HBDrew/PFD-and-AHRS/Docs/CONTROL_LOGIC_MAP.md

# TruTrak Vizion — Control Logic Map (v0.1)

**Status:** Working draft / reverse-engineering in progress
**Purpose:** Behavioral specification and test oracle for a modern, drop-in
replacement for the 2‑1/4" round and flat‑pack Vizion autopilot.
**Source of truth:** `TT AP Sources/` (Freescale 68HCS12 assembly, DigiFlight /
Sorcerer / Vizion‑380 lineage, version era ≈ A.43, 2003–2011).

> Citations below are `File:line` against the uploaded `TT AP Sources/` tree.
> Line numbers are from the version reviewed and should be re-verified when the
> sources are vendored into this repo.

**Companion deep-dives:**
- [`VERTICAL_CONTROL_LAWS.md`](VERTICAL_CONTROL_LAWS.md) — vertical axis in full
- [`STEPPER_OUTPUT_STAGE.md`](STEPPER_OUTPUT_STAGE.md) — command→phases servo chain
- [`SERVO_TORQUE_CONTROL.md`](SERVO_TORQUE_CONTROL.md) — torque/current control
- [`EEPROM_PARAMETER_MAP.md`](EEPROM_PARAMETER_MAP.md) — persisted parameter set

---

## Source provenance & build target (important)

This is a **single unified TruTrak codebase, target-selected at build time** — the
same source historically built DigiFlight II, **Sorcerer**, Model 100, RV-10AP and
Vizion (changelog: "v2.09 Merge the vertical mode code DFII/Sorcerer"). The shared
engine (`DFCMain.asm`, `DFC_IRQ.asm`, `p20Hz.asm`, `AD7714.asm`, `EEPROM.asm`, …)
contains **all** the control logic for every product, including Sorcerer.

**What selects a product is the per-target `Switches.asm`** (INCLUDEd at build):
it sets `PRODUCT_ID`, form-factor flags, `NAVMODE`, the switch/display layout and
pin maps, and *macro-generates* the `LM_*`/`VM_*` mode constants. This package
ships **only two target files, both Vizion 380**:

| Target file | PRODUCT_ID | Name |
|---|---|---|
| `Vizion 380 Flat/Switches.asm` | 1 | `[VZ380F]` |
| `Vizion 380 Round/Switches.asm` | 49 | `[VZ380R]` |

There is **no `Sorcerer/Switches.asm`** in this package. Sorcerer build knobs are
still visible (`EEDEFINES.h` `SORCERERNUMBER` calibration sets; an `IFDEF SKYPILOT`
path), but the Sorcerer *target configuration* (its product ID, panel switch
matrix, display driver, pin assignments) is not included.

**Consequence for this spec:**
- The **mode encodings and all control laws are target-independent** (same
  macro-generated constants, same math) — they apply to Sorcerer unchanged.
- **Target-specific citations here reflect the Vizion 380 Flat build** — notably
  pin/port maps (e.g. `MC33291` on `PTH.3`) and the switch/display layout. A
  Sorcerer (or other) target could differ in those.
- Building/analyzing the Sorcerer *target* would require its own `Switches.asm`.
  Open item: obtain it, then diff against the two VZ380 targets to enumerate the
  pin/switch/display/feature deltas.

---

## 0. Design intent for the revival (decisions locked)

These constraints frame every entry in this document. The map exists to make a
**behavioral port** possible, not a redesign.

| # | Decision | Rationale |
|---|---|---|
| D1 | **Preserve the rate-based inner loop.** Command a *turn rate* / *pitch rate*, close the inner loop on a rate signal. | Proven, robust, drives a stepper-through-slip-clutch well, and is the basis of "behaves like a Vizion." |
| D2 | **Attitude is a bounded *protection* layer only** — bank/pitch limiting, envelope, wings-level recovery. Never the primary control reference. | Keeps cost low, keeps the box source-agnostic, avoids re-tuning the whole feel. |
| D3 | **Keep the stepper servo drive.** Inherit the installed plant (stepper + clutch + cable + airframe) and harness/connector. | Required for true drop-in; the output stage ports over largely intact. |
| D4 | **Talk to anything.** Preserve all existing steering/deviation inputs (RS‑232 NMEA, ARINC‑429, discrete/analog CDI). | Rate-command interoperates with any GPS/EFIS that emits a steering or deviation signal. |
| D5 | **Preserve the tuned parameter set.** Gains encode years of flight tuning. | The port must carry gains + units forward verbatim, then re-scale deliberately. |
| D6 | **Ship setup UNLOCKED.** Remove the `EnableSettings == 10` gate — all setup menus directly accessible (via a modern menu, no button-hold handshake). | Baseline is **PV.40**; drop the "secret code." See "Setup-mode access" below. |

**Baseline: PV.40 (`pv.40` branch)** — chosen per
[`BASELINE_COMPARISON_PV40_vs_VZ15.md`](BASELINE_COMPARISON_PV40_vs_VZ15.md).

### Setup-mode access (the "secret code") — D6

PV.40 gates the advanced setup menus behind a parameter `EnableSettings`
(EEPROM `$0C`, def. `ENABLESETTINGS`). `DFCMain.asm:887` `enterSetup`:

- Knob pressed → **basic** setup (`EM_OFF`).
- `EnableSettings == 10` **and** hold **TRK/MODE** → lateral setup (`EM_LAT_FIRST`).
- `EnableSettings == 10` **and** hold **ALT** → vertical setup (`EM_VERT_FIRST`).
- `EnableSettings != 10` → locked (`noModeEvent`).

Default builds ship `ENABLESETTINGS = 0` (locked); **RV10 & Cessna-172 (certified)
ship `= 10` (unlocked from factory)** — hence those units felt "open." `S1_DIAG`
(diagnostics, `EM_DIAG`) is a separate gate.

**Revival:** delete the `CPD #10 / BNE` gate so setup is always reachable. (To
unlock a stock PV.40 binary on the bench: write `10` to EEPROM `$0C`.)

Target processing: modern Cortex‑M4F/M7 class MCU (FPU) → retire hand-rolled
fixed-point and the assembly RTOS in favor of C + float + small RTOS/superloop,
**while preserving the control-law structure and gains**.

---

## 1. System architecture (as-built)

Hand-written assembly on a Freescale 68HCS12 (16-bit, banked/paged flash), with
a **preemptive priority RTOS** written in assembly.

```mermaid
flowchart TB
  subgraph SENSE[Sensing]
    RG[Rate gyros: roll/pitch/yaw<br/>rollValue 163.84 cnt/deg/s]
    AD[Air data: IAS, Altitude, iVSI]
    GPS[GPS: track, gnd speed, xtrk, brg/dist]
    ARINC[ARINC-429 in: 121 roll-steer,<br/>320 mag hdg, 325 roll angle, alt]
    CDI[Analog/discrete CDI + rate]
  end
  subgraph EST[Estimation]
    DG[Electronic DG<br/>4-byte fraction-of-circle]
    MAG[magCircle]
    FILT[20 Hz filters, iVSI, LPF_1]
  end
  subgraph LOGIC[Mode logic]
    SM[Lateral + Vertical<br/>mode state machines]
  end
  subgraph LAW[Control laws]
    LAT[calcCommand -> turnCmd<br/>100 = 1 deg/s]
    VRT[vertical -> pitchCmd<br/>100 = 1 deg/s]
  end
  subgraph OUT[Servo output stage]
    RV[SetRollVel / SetPitchVel<br/>vel+pos, 2-pole LPF, activity,<br/>hysteresis, backlash comp]
    DRV[Stepper drive<br/>legacy DAC/PWM -> CAN motor msg]
  end
  SENSE --> EST --> LOGIC --> LAW --> OUT --> Steppers
  RG --> LAW
```

**Concurrency (RTOS):** `Kernel.inc` defines a TASK struct (linked ready list,
timer wakeup list, per-task page register), semaphores (`MAX_SEM`), and
`createTask/signal/wait/setPri`. Tasks coordinate through semaphores rather than
one superloop.

| Task / ISR | Rate | Role |
|---|---|---|
| Timer ISR (`tim_int`) | ~250 Hz (4 ms) | Servo velocity loop, switch debounce, timers |
| 20 Hz filter (`Start20Hz`, `p20Hz.asm`) | 20 Hz | Low-rate filtering, GPSS buffer, mode housekeeping |
| Main loop (`mainLoop`, `DFCMain.asm`) | event/10 Hz | Mode logic, display, `calcCommand` |
| RS‑232 out (`StartOutput`) | streaming | Status/telemetry |
| GPS monitor (`GPSMonitor*.asm`) | per-sentence | Parse NMEA / protocol |
| CAN (`CAN.asm`) | per-msg | Smart-servo motor messages |
| Talker (`Talker.asm`) | event | Audio annunciation |

*Timer tick inferred from `DFC_IRQ.asm` "number of 4mSec periods" comments — verify exact prescaler.*

---

## 2. Mode model (the `mode` byte)

> **PV.40 baseline update:** on the chosen PV.40 baseline, `VERTICAL_MASK` is
> **`$F0`** (vertical field = bits 4–7) and there are extra modes — lateral
> `LM_DYNON/LM_AEP/LM_ASPEN`, vertical `VM_DYNON/VM_EXT_ALT`. See
> [`PV40_BASELINE_ADDITIONS.md`](PV40_BASELINE_ADDITIONS.md) §1–2. The encoding
> below reflects the 2011 baseline and still holds for the common modes.

A single byte `mode` is bit-packed (`Vizion 380 Flat/Switches.asm:38-63`):

```
 bit 7   bits 6..4          bits 3..0
 [ E ] [ vertical mode ] [ lateral mode ]
   |         |                  |
   |         |                  +-- LATERAL_MASK = $0F
   |         +--------------------- VERTICAL_MASK = $70
   +------------------------------- entry/display-mode flag ($80)
```

### 2.1 Lateral modes (`LM_*`, sequential 0..10)

| Val | Mode | Meaning |
|----:|---|---|
| 0 | `LM_NONE` | AP off; initial until CWS or ENT |
| 1 | `LM_CWS` | AP off; CWS pressed, capturing gpsTrk |
| 2 | `LM_TRK` | Track mode — follow selected ground track (**universal fallback**) |
| 3 | `LM_DG` | External DG/HSI — follow external turn command |
| 4 | `LM_GPSNAV` | GPS NAV, CDI centered to waypoint |
| 5 | `LM_GPSPOST` | GPS NAV, near/past waypoint |
| 6 | `LM_GPSS` | GPS Steering — follow ARINC/RS‑232 bank command |
| 7 | `LM_NAV_PRE` | Intercepting NAV CDI via calculated vector |
| 8 | `LM_NAV_POST` | NAV CDI captured, hold centered (low gain) |
| 9 | `LM_REV_PRE` | Like NAV_PRE, steer *away* from needle |
| 10 | `LM_REV_POST` | Like NAV_POST, steer *away* from needle |

Free-gyro **wing-leveler / bank-hold** is a sub-behavior of the `selTrk` path
(`DoSelTurn`) when no GPS/mag reference is present and `selBank ≠ 0`
(`DFCMain.asm:1688`).

### 2.2 Vertical modes (`VM_*`, value = index << 4)

| Mode | Meaning |
|---|---|
| `VM_NONE` | No vertical mode |
| `VM_HOLD` | Altitude hold |
| `VM_AS_SELECT` | Climb/descend to selected alt at selected airspeed |
| `VM_VS_SELECT` | Climb/descend to selected alt at selected ft/min |
| `VM_SPEED` | VS entered manually while in hold |
| `VM_CAPTURE` | Following glideslope (GS) |
| `VM_VNAV` | Selected alt at selected distance |
| `VM_GPSS` | External unit giving pitch/vertical command (VGPSS) |

---

## 3. Lateral mode state machine

Events come from buttons/knob/timeouts via the action table
(`DFCMain.asm:383-399`): `altAction` (AP), `GPSSAction` (GPSS), `NAVAction`,
`REVAction`, `TRKAction`, `modeAction`, `rotAction` (knob turn),
`knobAction` (ENTER), `revertAction` (idle timeout), `vsUp/vsDn/HOLD/ASEL/VNAV`.

```mermaid
stateDiagram-v2
  [*] --> OFF
  OFF: LM_NONE (AP off)
  CWS: LM_CWS (capturing track)
  OFF --> CWS: CWS switch
  CWS --> TRK: release (capture gpsTrk)
  OFF --> TRK: AP engage

  TRK: LM_TRK (fallback home)
  TRK --> TRK: knob rotate (set selTrk)
  TRK --> GPSS: GPSS btn (if steer cmd valid)
  TRK --> DG: ext DG selected
  TRK --> NAV_PRE: NAV btn
  TRK --> REV_PRE: REV btn
  TRK --> GPSNAV: GPS NAV armed

  GPSS --> TRK: steer cmd lost (snapshot DG -> selTrk)
  GPSNAV --> GPSPOST: near/past waypoint
  GPSNAV --> TRK: guidance lost
  GPSPOST --> TRK: guidance lost

  NAV_PRE --> NAV_POST: CDI intercept
  NAV_POST --> TRK: NAV lost
  REV_PRE --> REV_POST: CDI intercept
  REV_POST --> TRK: NAV lost

  DG --> TRK: ext DG lost / mode change
  TRK --> OFF: disconnect
  GPSS --> OFF: disconnect
  NAV_POST --> OFF: disconnect
```

**Invariants worth preserving verbatim:**

- **TRK is the safe harbor.** Any loss of GPSS/GPS‑NAV/NAV guidance snapshots the
  current DG heading into `selTrk` and reverts to `LM_TRK`
  (`DFCMain.asm:1660-1670`, `lostLatGuidance`). The aircraft keeps flying its
  current heading rather than dropping the servo.
- **Lateral↔vertical coupling:** setting *any* lateral mode while in `VM_CAPTURE`
  (glideslope) forces vertical to `VM_HOLD` (`SetLatMode`, `DFCMain.asm:5198`).
- `SetLatMode` toggles only the lateral nibble and always clears the entry-mode
  bit — modernized code must keep mode fields independent.

---

## 4. Lateral control law (`calcCommand`, `DFCMain.asm:1233`)

Output is `turnCmd` (signed, **100 = 1 °/s**, positive = turn right),
`DFC_IRQ.asm:203`. The active branch depends on lateral mode:

1. **Selected-track / DG (`DoSelTurn`, `DoDGTurn`)**
   - Error = `selTrk − DG` in circle units.
   - Low-pass filter the error (`LPF_1`, `TrkError_LPF`), filter constant
     **scheduled on IAS** (`DGCONST` from `currIAS`, `DFCMain.asm:1454+`).
   - Add a **track-rate (derivative) term**, zeroed when |error| > 45°
     (`$2000`/`$E000` guards) to avoid nonsense during large captures.
   - Gain via lookup `TRKRATEGAINtbl`; convert to command by ×`#3584/65536`
     (≈ 7/128) → command 300 at 30° error.
2. **GPSS (`DoGPSSTurn`, `DFCMain.asm:1560`)**
   - Take external bank command `gpssRoll`, scale by `gpssGain/8`, saturate to
     ±8192.
   - Add a rate term now **airspeed-scheduled**: gain = `TAS[kt·8]/60`
     (`DFCMain.asm` 2.36B block), saturate to ±8192.
   - If ARINC label 325 (roll angle) is present, form a closed-loop bank error
     (`DoGPSSErrorTurn`).
3. **NAV / REV (LOC/VOR)** add a **rate (CDI-movement) term** beyond the bank
   limiter (`addNavRate`, `DFCMain.asm:~1990+`): LOC uses `locRateGain`; VOR uses
   4× fixed radio rate with a 1 °/s clip for station passage; REV reverses sense.
4. **Cross-track intercept geometry:** intercept angle = `arcSin(64·xTrkErr[nm]/gs[kt])`,
   `xTrkErr` clipped to 127 nm to prevent overflow (`DFCMain.asm:2794`).

**Bank limiter** (applied to the command, not attitude), `DFCMain.asm:1782-1830`:

| `MaxBank` | Turn-cmd clamp | ≈ bank @ 200 kt |
|---|---|---|
| 0 (LO) | 225 | ~22° |
| 1 (MED)| 300 | ~25° |
| 2 (HI) | 375 | ~28° |

GPSS uses a separate `gpssMaxBank` (~25°).

---

## 5. Vertical control law (summary)

> **Full treatment:** [`VERTICAL_CONTROL_LAWS.md`](VERTICAL_CONTROL_LAWS.md) —
> the VS-rate pipeline, iVSI estimator, `pitchAdj` trim integrator, all modes
> (ALT/VS/AS-hold/VNAV/GS/VGPSS), envelope protection, and two comment-vs-code
> discrepancies to reproduce.

- **ALT HOLD:** `altErr = selAlt − currAlt`, scaled by user `altGain` (0..8),
  combined with **iVSI** (integrated/inferred vertical speed, computed
  proportional to altitude), plus turbulence filtering → `pitchCmd`.
- **VS / VS_SELECT:** fly a selected ft/min toward selAlt.
- **VNAV:** compute required VS to reach `selAlt` at `selDist`.
- **GS CAPTURE (`VM_CAPTURE`):** arm/couple timers (`gsTimer`, `vgsTimer`),
  go-around pitch-up on leaving coupling (`gaTimer`); auto-drops to HOLD on
  lateral mode change.
- **VGPSS (`VM_GPSS`):** vertical steering from ARINC deviation.

---

## 6. Servo output stage (`SetRollVel` `DFC_IRQ.asm:1888`, `SetPitchVel`)

This is the part that ports over most directly (D3). Per axis:

1. Scale commanded velocity by **activity setting** (`latGain`/`vrtGain`, 0..12,
   log-encoded offset-by-6) via `actTable`.
2. Saturating multiply (hand-rolled overflow guard `rOVF`).
3. **2-pole low-pass** (`rv1`, `rv2`).
4. **Servo velocity limiter** (`servoLimit`).
5. **Deadzone / hysteresis:** 50-count hysteresis to suppress noisy dither.
6. **Lost-motion / backlash compensation:** on a commanded direction reversal,
   inject `16·sign(dir)·lostMotion` for ~400 ms (`rDZ_*`). This compensates gear
   backlash in the stepper/clutch drive — **must be reproduced.**
7. Result → `rollVel`/`pitchVel`; **position = ½∫velocity** (`rollPos`/`pitchPos`).
8. Emit to drive — **this build drives BOTH paths every servo tick, in parallel**
   (confirmed):
   - **Stepper (legacy, the one we need for 2‑1/4"/flat-pack):** `DoMotors`
     (`DFC_IRQ.asm:2193`, called from the ISR at `:3059`) integrates velocity →
     `rollPos`/`pitchPos`, indexes the 8-entry **gray-code phase table**
     `grayTable` (half-step aware), merges roll (high nibble) + pitch (low
     nibble) into one byte, and shifts it out over SPI0 to an **MC33291 octal
     low-side driver** that energizes the stepper phases. Includes a v2.20c
     inrush-limiting sequence on 0→1 phase transitions (`SERVO_PORT` holds the
     previous pattern for ~1 µs).
   - **CAN smart-servo (later designs):** `MotorCANMsgBuffer` populated in
     `SetRollVel` + `DoMotors`; transmitted via `CAN_TxMessage`
     (`CAN.asm:598`, called from `DFCMain.asm:1096/8789/8888`).
   - **Oldest analog drive retired:** `DAC_67Out` servo-voltage path is commented
     out; the DAC survives only for the yaw-damper output.

> **Full bit-level treatment of this stage:** see
> [`STEPPER_OUTPUT_STAGE.md`](STEPPER_OUTPUT_STAGE.md) — inner rate loop,
> velocity conditioning (activity table, LPF, limiter, hysteresis, backlash),
> position integration, gray-code phase output, MC33291 mapping, and the
> modern-hardware reproduction plan.
>
> **Backward-compat scheme (confirmed):** not a stepper-vs-CAN config switch —
> both drivers run unconditionally from the same velocity/position math each
> tick, and the airframe harness consumes whichever it is wired for. The `config`
> bits gate yaw damper / alt selector / ext-DG only, not servo type. **This is
> the correct both-worlds source version.** For the revival, replicate the
> stepper chain: **velocity → ½∫ position → gray-code phase table → phase
> driver** (MC33291 or modern equivalent).

---

## 7. Units & fixed-point dictionary

The single most portable asset. Every constant below must survive the port.

| Quantity | Representation | Notes |
|---|---|---|
| Heading / track / bearing | **circle units**: 65536 = 360° | `DG` is 4-byte fraction of circle; `BrgToCir`/`CirToHdg` convert |
| Turn / pitch command | signed, **100 = 1 °/s** | `turnCmd`, `pitchCmd` |
| Roll rate (gyro) | **163.84 counts/°/s**, signed | `rollValue` |
| Airspeed | **kt · 8** | `currIAS`, `currTAS` (since v2.16) |
| Altitude | **ft MSL**, signed (4 ms-bits = negative) | `currAlt`; `filterAlt` carries fraction |
| Baro | inHg · 100 | `baroSet` (2992 = 29.92) |
| Activity / gain | 0..12, **log offset-by-6** (6⇒×1, >6⇒×9/8, <6⇒×7/8) | `latGain`, `vrtGain` |
| Cmd→bank scale | `×3584/65536` (≈7/128) | 300 cmd ≈ 30° track error |
| GPSS saturation | ±8192 | repeated inline (candidate for one routine) |

---

## 8. Envelope protection & interlocks

The safety layer — where attitude protection (D2) will augment, not replace.

- **Airspeed envelope** (vertical modes, `DFCMain.asm:2325-2445`, `CAS_1:3702`):
  climbing won't allow IAS < `minAS` (stall guard); descending won't allow
  IAS > `maxAS` (overspeed). `absMaxAS = 399 kt`. `minAS` not enforced below
  ~50 kt actual (avoid ground false-trip).
- **MIN AS annunciation also drops the yaw damper** (`HISTORY` 2.19).
- **Gyro centering hold-off:** in TRK, when |command| > 250 for a sustained
  maneuver, set `turnTimer` (150 → ~30 s) so the roll gyro doesn't capture an
  offset mid-turn (`DFCMain.asm:1869+`). *This kludge is a prime candidate to
  replace with a real attitude reference under D2.*
- **Disconnect / CWS** paths; press-and-hold semantics (`cwsSem`, `yokeSem`).

**Modernization note (D2):** add attitude-based bank/pitch limiters and a
wings-level recovery as an outer *clamp* on `turnCmd`/`pitchCmd`, and replace the
`turnTimer` centering hack with attitude-referenced centering. Attitude never
becomes the command reference.

---

## 9. I/O & interfaces (for "talk to anything", D4)

| Interface | Direction | Content |
|---|---|---|
| RS‑232 NMEA (`GPSMonitor*.asm`) | in | GPS track, gnd speed, xtrk, brg/dist |
| ARINC‑429 (`arinc_int`) | in | 121 roll steering, 320 mag hdg, 325 roll angle, selected/baro alt |
| Analog/discrete CDI | in | LOC/VOR deviation + rate (`ATD0DR2H`) |
| External DG/HSI | in | `ATD0DR4H`, `dgGain` |
| RS‑232 status (`StartOutput`) | out | Mode/airspeed/trim telemetry |
| CAN (`CAN.asm`) | out | Smart-servo motor messages |
| Audio (`Talker.asm`) | out | Voice annunciation |
| Display + knob/buttons | i/o | UI |

---

## 10. Open questions / next revisions

- [x] **Servo drive:** RESOLVED — this build drives both the legacy gray-code
      stepper (MC33291/SPI) and CAN smart-servo in parallel every tick; harness
      picks. Confirmed correct both-worlds source. Revival targets the stepper
      chain (§6).
- [ ] Vendor the `TT AP Sources/` tree into the repo (or a ref/ subfolder) so
      citations resolve and diffs are traceable — confirm IP/licensing first.
- [ ] Full **parameter/EEPROM map** (`EEDEFINES.h`, `EEPROM.asm`): every gain,
      offset, limit with address + default + units.
- [ ] v0.2: complete **vertical** state machine + laws (VNAV, GS capture, VGPSS).
- [ ] Confirm timer-tick rate/prescaler (assumed 4 ms / 250 Hz).
- [ ] Enumerate exact button/event → transition guards from the action routines.
- [ ] Catalog target variants (Vizion 380 Flat/Round, Model 100, RV‑10) and their
      conditional-assembly differences.

## 11. Old → new mapping (guiding the port)

| As-built (68HCS12 asm) | Revival (Cortex-M4F, C) | Under decision |
|---|---|---|
| Rate gyros | MEMS IMU rate channels (better source, same law) | D1 |
| No attitude ref; `turnTimer` centering hack | AHRS attitude → protection clamps + centering | D2 |
| Hand fixed-point (circle units, kt·8) | float, but **keep gains & scaling documented** | D5 |
| Assembly RTOS + semaphores | small RTOS / timed superloop | — |
| DAC/PWM→CAN stepper drive | match installed-base drive exactly | D3 |
| Repeated inline saturation | one vetted `saturate()` | maintainability |
| Demo/`fMode` hooks in flight path | compiled out / separate build | safety |

---

*v0.1 — extracted from `TT AP Sources/`. Sections §5, §8, §10 flagged for
expansion. Treat every gain/threshold here as authoritative-to-verify against the
source before it drives code.*
