HBDrew/PFD-and-AHRS/Docs/ADSB_IN.md

# ADS-B IN — Traffic (and FIS-B weather) on the PFD

This document describes the ADS-B IN feature: how the display ingests
traffic, how to wire up the Nooelec NESDR Nano 2 dual-band receiver, and
what is implemented vs. planned.

## What it does

Live aircraft traffic is drawn on the moving-map inset of both displays
(Pi Zero MFD and Pi 4) as TCAS-style diamonds with a heading leader and a
relative-altitude data tag. Targets are colour-coded by threat:

| Colour | Class | Meaning |
|---|---|---|
| Cyan (hollow diamond) | other | has a position, outside the proximate envelope |
| Amber (filled) | proximate | within 6 NM **and** 1200 ft |
| Red (filled) | alert | within 3 NM **and** 600 ft, or the source flagged a traffic alert |

The data tag reads relative altitude in hundreds of feet with a trend
arrow, e.g. `+12↑` (1200 ft above and climbing), `−05↓` (500 ft below,
descending).

Toggle the layer at **Setup → Display → MAP LAYERS → TFC**.

## Architecture

The display side is **hardware-independent** — it speaks GDL90 over UDP,
the lingua franca of portable ADS-B receivers (Stratux, Sentry, GDL90
bridges). Nothing in the PFD knows about SDR dongles.

```
 1090ES  ── NESDR ──►  readsb ───────┐
                                     ├─ SBS-1 :30003 ─► adsb_gdl90_bridge.py ──┐
 978 UAT ── NESDR ──►  dump978-fa  ──┘  (978 traffic folds into readsb too)    │
                                                                              GDL90/UDP :4000
 Internet aggregator  ──►  adsb_internet_feed.py  ───────────────────────────►│  (any/all
 (airplanes.live / opensky, via Wi-Fi / Starlink)                             │   sources fan in)
                                                                              ▼
                                            shared/adsb.py  (ADSBClient: UDP listener,
                                            target table, staleness aging, snapshot)
                                                          │
                                            shared/gdl90.py (deframe + CRC + decode)
                                                          │
                              pfd.py _update_traffic()  → disp["traffic"]
                                                          │
                              moving_map.render(traffic=…) → diamonds
```

### Modules

| File | Role | Tested by |
|---|---|---|
| `shared/gdl90.py` | GDL90 framing (0x7E / byte-stuffing / CRC-16) + message decoders (Traffic 0x14, Ownship 0x0A/0x0B, Heartbeat 0x00, FIS-B uplink 0x07). Also an encoder for tests/bridges. | `shared/test_gdl90.py` |
| `shared/adsb.py` | `ADSBClient` threaded UDP listener (SSEClient-style counters), target table with aging, `relative()` range/bearing/rel-alt, `threat_level()`, `demo_targets()`. | `shared/test_adsb.py` |
| `tools/adsb_gdl90_bridge.py` | readsb/dump1090 SBS-1 (TCP 30003) → GDL90/UDP bridge using the encoder above. | `--selftest` |
| `tools/adsb_internet_feed.py` | Internet ADS-B aggregator → GDL90/UDP feed (test source + Starlink in-flight source). | `--selftest` |
| `tools/install_adsb.sh` | Installs rtl-sdr + **readsb** (1090) + the GDL90 bridge systemd unit. (978 via `install_dump978.sh`.) | — |

Because every source emits the same GDL90/UDP, they are interchangeable and
can even run side by side — a local SDR receiver, the SBS→GDL90 bridge, and
the internet feed all just fan into the one listener on :4000.

### Display wiring

`pfd.py` (both variants) starts an `ADSBClient` at boot when
`cs["adsb_enabled"]` is set, and once per frame calls `_update_traffic()`,
which snapshots the listener (or `adsb.demo_targets()` in `--demo`),
relativises each target against the current ownship fix, classifies its
threat, sorts nearest-first, and stores the result in `disp["traffic"]`.
`moving_map.render(traffic=…)` draws it, gated by `ds["map_show_traffic"]`.

Link diagnostics are mirrored into `cs["adsb_online"|"adsb_rx"|"adsb_err"|
"adsb_last_err"|"adsb_uplink"]` (runtime-only, not persisted).

## Hardware setup (Nooelec NESDR Nano 2 dual-band)

The bundle is two RTL-SDR dongles plus 978/1090 antennas. Run the receiver
on the display Pi, a dedicated Pi (a Pi 5 has ample headroom), or point the
display at an existing Stratux on the network.

```bash
sudo bash tools/install_adsb.sh       # rtl-sdr + readsb (1090) + GDL90 bridge
sudo bash tools/install_dump978.sh    # 978 UAT decoder + FIS-B weather bridge
sudo bash tools/enable_978_traffic.sh # fold 978 traffic into readsb's :30003
sudo reboot                           # so the DVB-T driver blacklist takes effect
```

Give each dongle a distinct USB serial so the decoders grab the right band:

```bash
rtl_eeprom -d 0 -s 1090          # dongle on the 1090 antenna
rtl_eeprom -d 1 -s 978           # dongle on the 978 antenna
```

The 1090 decoder is **readsb** (wiedehopf's installer) — `dump1090-fa` isn't
reliably packaged for current Raspberry Pi OS (Debian trixie / Pi 5). readsb is
pinned to the 1090 dongle via `RECEIVER_OPTIONS="--device 1090 …"` in
`/etc/default/readsb` and publishes SBS-1 on TCP 30003, which the bridge turns
into GDL90/UDP :4000. dump978 (serial `978`) decodes the 978 band.

> **Bringing up a fresh / dedicated receiver Pi?** See `BENCH_TEST_PI5_ADSB.md`
> for the full layered procedure (hardware → decoders → bridge → display), the
> LAN-broadcast gotcha, and the two failures seen on a real Pi 5 bring-up.

Verify:

```bash
systemctl status adsb-gdl90.service
python3 tools/adsb_gdl90_bridge.py --selftest
```

## Testing without hardware

```bash
python3 shared/test_gdl90.py     # decoder unit tests
python3 shared/test_adsb.py      # listener + geometry + UDP loopback
python3 pi4/pfd.py --demo --sim  # synthetic traffic orbits the demo aircraft
```

### Testing with real internet data

`tools/adsb_internet_feed.py` pulls live aircraft from a public ADS-B
aggregator and emits them as GDL90/UDP — so you can see *real* traffic on
the map with no SDR and no Pico. Run the display and the feed together:

```bash
# terminal 1 — the PFD (demo flies the Sedona pattern; live traffic wins
# over the synthetic targets, so point the feed at the demo location)
python3 pi4/pfd.py --demo --sim

# terminal 2 — feed real traffic within 80 NM of the demo position
python3 tools/adsb_internet_feed.py --lat 34.8697 --lon -111.7610 --radius 80
```

Point it somewhere busy (`--lat 33.94 --lon -118.40` for KLAX) to stress the
renderer with dozens of targets. Sources: `airplanes_live` (default),
`adsb_lol`, `adsb_fi`, `opensky` — none need an API key.

The "live wins over demo" rule (`_update_traffic`) means any real source —
internet feed, dump1090 bridge, or hardware receiver — overrides the
synthetic demo targets the moment frames start arriving.

## In-flight over Starlink / cabin Wi-Fi

With internet in the aircraft, the same feed becomes a real traffic source —
no receiver required. Run it on the display Pi and have it re-centre on your
own GPS so the query box follows the flight:

```bash
python3 tools/adsb_internet_feed.py --follow-ahrs http://192.168.4.1/events --radius 60
```

(Or install it as a systemd service alongside `adsb-gdl90.service`.)

**Advisory only.** Internet traffic depends on ground-station coverage and
connectivity — it lags a few seconds, has coverage gaps, and won't reliably
include UAT-only / non-transponder aircraft. It is **not** a substitute for
see-and-avoid or a certified traffic system. A local SDR receiver (the
Nooelec) gives better own-ship-relative traffic because it's direct
line-of-sight and works without internet; treat the internet feed as a
convenient backup / test source. Keep the poll interval ≥ 1 s out of
courtesy to the free aggregators.

## Implemented vs. planned

**Implemented (V5.4):**
- GDL90 decode + UDP ingest + target management (tested)
- Relative geometry + TCAS-style threat classification
- Traffic diamonds on both moving maps + TFC layer toggle
- dump1090 → GDL90 bridge + receiver installer
- Demo traffic generator

- Internet traffic feed (`tools/adsb_internet_feed.py`) — no-hardware test
  source and Starlink/cabin-Wi-Fi in-flight source; live traffic overrides
  the demo targets automatically.
- Traffic declutter — altitude-band (±2k/5k/10k) and range (5/10/20/40 nm)
  filters on Setup → Display; alert-class threats always survive.
- **Weather — METARs.** `shared/wx.py` polls aviationweather.gov for the
  current **map view** (not just the aircraft) — `WxClient` takes a
  `view_fn -> (lat, lon, radius)` and re-fetches when you pan far enough,
  zoom, or the periodic refresh is due (debounced so a drag doesn't spam the
  API). Query radius scales with zoom (`WX_RADIUS_ZOOM_K`, clamped
  `WX_MIN/MAX_RADIUS_NM`), so panning/zooming over CONUS loads weather for
  wherever you're looking. Flight-category station dots (green VFR / blue
  MVFR / red IFR / magenta LIFR) render on both maps. Tap a dot on the MFD
  for the decoded readout. Source-agnostic `disp["weather"]`.
- **Overlay quick-cycle** (`shared/mapoverlay.py`, unit-tested). Traffic
  stays on always (safety); a single on-map control cycles the heavy
  overlays one-at-a-time to keep the map readable and CPU low:
  **Airspace → Traffic → METAR → Winds → NEXRAD** (labels ASP / TFC / MET / WND / NEX).
  "Traffic" (TFC) is the traffic-only state — no heavy overlay added;
  traffic + your base map still show. On the Pi Zero MFD it's the button
  under the RNG label; on the Pi 4 inset it's the **bottom-left corner**
  (label shows the current state). Both drive the same `ds["map_show_*"]`
  booleans the Setup → Display pills (MET / NEX / ASP) use, so they stay
  consistent. The weather poller only runs while METAR/NEXRAD is the active
  overlay — no CPU/network spent on weather you're not looking at.

- **Weather — NEXRAD raster** (`shared/nexrad.py`). Composite reflectivity
  from the Iowa Environmental Mesonet WMS (free, no key), fetched for the
  current map view (same `view_fn` as METARs) and only while the NEXRAD
  overlay is active. Rendered **north-up** (no per-frame rotation — lowest
  CPU; aligned in north-up mode), georeferenced to its lat/lon bbox, blitted
  semi-transparent under the symbols. The scaled/dimmed surface is cached, so
  the per-frame cost is one blit; it's re-decoded only when a new image
  arrives (~5 min) or the zoom changes.
- **Weather declutters the base map.** While METAR, NEXRAD, or winds is the
  active overlay, the terrain tint and obstacle/tower symbols are suppressed —
  cleaner weather picture, and skipping the tint build is the biggest CPU
  saving the inset has.
- **Weather — TAF / AIRMET / SIGMET / NOTAM readouts.** Tapping a station on
  the MET page opens a picker with **METAR / TAF / AIRMET / SIGMET / NOTAM**
  tabs (scrollable, nearest-first, ON-ROUTE flags). TAFs + AIRMET/SIGMET come
  from aviationweather.gov (AWC); graphical AIRMET/SIGMET hazard polygons are
  shaded and tappable. NOTAMs come from the **FAA NMS-API** (two-step OAuth2;
  preprod `api-staging.cgifederal-aim.com`, prod `api-nms.aim.faa.gov`) — needs
  a `client_id`/`client_secret` (**NOTAM KEY** / **NOTAM SECRET**) plus a
  **NOTAM ENV** (preprod default) entered on the Connectivity screen; absent a
  key the NOTAM fetch is a harmless no-op. NOTAMs use their own **tight,
  zoom-following query radius** (`NOTAM_MIN/MAX_RADIUS_NM`, ~10–40 nm) rather
  than the wide weather radius, so a tap over a metro returns a local handful
  rather than every NOTAM for hundreds of miles. **Shared over screen-sync**
  (`KIND_NOTAMS`): one keyed display feeds NOTAMs to peers that have no key, and
  the key itself can be **pushed to every display** (`KIND_NOTAMCREDS`) by
  entering it once in Connectivity — same model as winds aloft.
- **Weather — winds aloft (WND).** GFS pressure-level winds from Open-Meteo
  (`gfs025`, free, no key), capped at 18,000 ft. Cached as a national grid
  split into 6 zones, fetched on the ground one zone at a time, written to disk
  (`data/winds/conus_winds.json`), and re-pulled only when a zone is > 3 h
  stale. Rendered as standard wind barbs + temperature at a selectable altitude
  (3k–18k) and forecast time (NOW/+Nh). **Shared between displays** over the
  screen-sync UDP link (`KIND_WINDS`): one display with internet feeds the
  whole panel so the others make zero Open-Meteo calls (per-IP rate-limit fix).
- **Traffic status + collision alert.** On-screen `ADS-B <mode> R<n> I<n>` and
  `WX <mode> R<n> I<n> <age>` status lines (tap to cycle RADIO/AUTO/INET); a
  flashing red **TRAFFIC** banner and (Pi 4) a **"Traffic, Traffic"** voice
  callout when a new target enters the alert envelope (≤ 3 NM and ≤ 600 ft),
  edge-triggered, rate-limited. Pi Zero is visual-only.

### FIS-B (978 UAT) weather — radio-primary, internet-bonus

Weather over the radio, no internet needed — the same source model as traffic.
The 978 dongle (serial `978`) is decoded by **dump978**; its raw uplink frames
(`+…` lines) are bridged to GDL90 0x07 on :4000, where `ADSBClient` folds them
into `fisb.FisbWeather`.  `_update_weather()` merges that over the internet
METARs (radio wins per station) and the MFD WX status line shows the split.

```
 978 UAT ── NESDR ──► dump978-fa ── raw :30978 ──► dump978_gdl90_bridge.py ──► GDL90/UDP :4000
```

| File | Role | Tested by |
|---|---|---|
| `shared/fisb.py` | FIS-B decode (DLAC text, info-frame walk, APDU), METAR parse, `FisbWeather` store, `merge_metar_sources`. | `shared/test_fisb.py` |
| `tools/dump978_gdl90_bridge.py` | dump978 raw `+` uplink → GDL90 0x07 / UDP. `--emit-test-wx` injects synthetic METARs; `--selftest` round-trips. | `--selftest` |
| `tools/install_dump978.sh` | Installs dump978-fa on serial 978 + the bridge as systemd units, alongside the untouched 1090 stack. | — |
| `tools/enable_978_traffic.sh` | Adds a `uat_in` net-connector so readsb folds dump978's 978 *traffic* into its existing SBS/GDL90 output (no new decode path). | — |
| `tools/fisb_sim.py` | Ground FIS-B simulator — broadcasts a realistic AZ weather field (real idents, all categories, 2 towers) as GDL90 to :4000 for building/testing the WX screens with no radio. | `--selftest` |

Enable on a receiver Pi: `sudo bash tools/install_dump978.sh`.  Stage 1 is text
weather (METAR/SPECI); winds/AIRMET/SIGMET/NOTAM text and the FIS-B NEXRAD
raster are the next stages.

**Receiving-station cue:** each FIS-B uplink frame carries the transmitting
ground station's own position (the 8-byte UAT header), so the MET overlay draws
a teal transmitter triangle ("FISB <age>s") at the tower(s) currently being
heard.  No station database needed — it's decoded straight from the frame, and
it doubles as the live reception indicator (a symbol here = FIS-B arriving now).
True RSSI stays at the receiver (it's dump978 metadata, not in the broadcast,
and the display may be a different Pi) — recency/count is the cross-network
strength proxy.

**978 traffic (bonus):** dump978 also receives UAT *traffic* (the `-` downlink
frames).  `sudo bash tools/enable_978_traffic.sh` points readsb at dump978's
raw port (`uat_in`), so those aircraft merge into readsb's SBS output and reach
the display over the existing `adsb-gdl90` bridge — 978 traffic on the same path
as 1090, no extra decoder.

**Planned:**
- Optional track-up rotation for the NEXRAD raster (cached per heading) if
  the north-up-in-track-up mismatch proves distracting.
- FIS-B **radio** NEXRAD block raster decoded into the existing nexrad surface
  (the internet NEXRAD path is done; the over-the-air block decode is next).
- Connectivity-screen ADS-B LINK row (diagnostics are already plumbed in
  `cs["adsb_*"]`).
- Direct 978 UAT path in the bridge (currently folded via the SBS feed).

(Winds aloft, AIRMET/SIGMET, NOTAM text, the METAR/TAF readout picker, and the
on-screen traffic status + collision alert — all previously listed here — are
now **implemented**; see the list above.)
