HBDrew/PFD-and-AHRS/Docs/IMG_0257.png

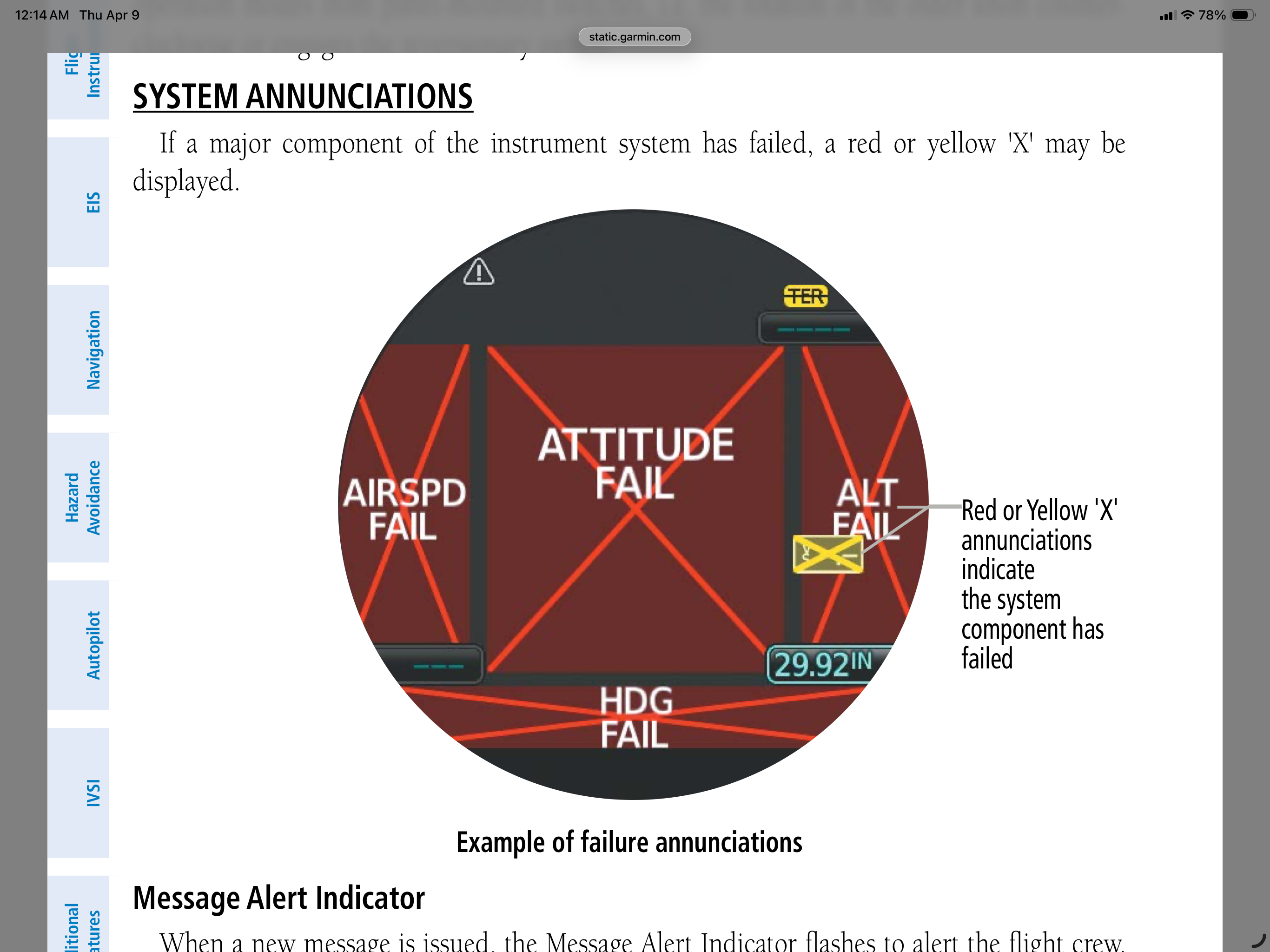
Docs/IMG_0257.png
