HBDrew/PFD-and-AHRS/Docs/IMG_0258.png

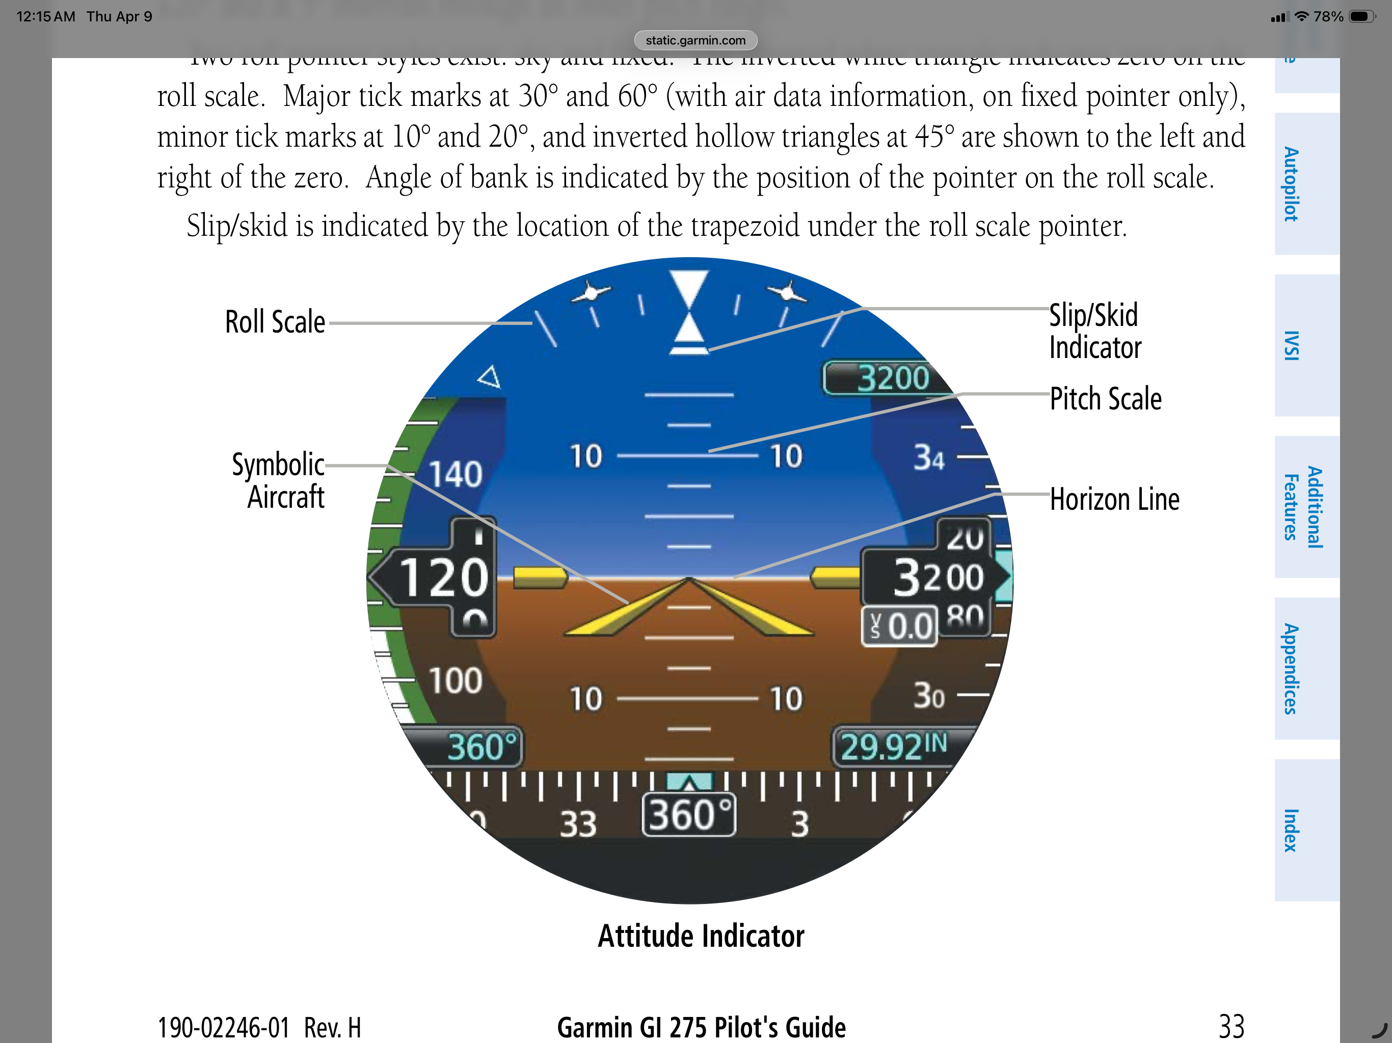
Docs/IMG_0258.png
