HBDrew/PFD-and-AHRS/Docs/IMG_0259.png

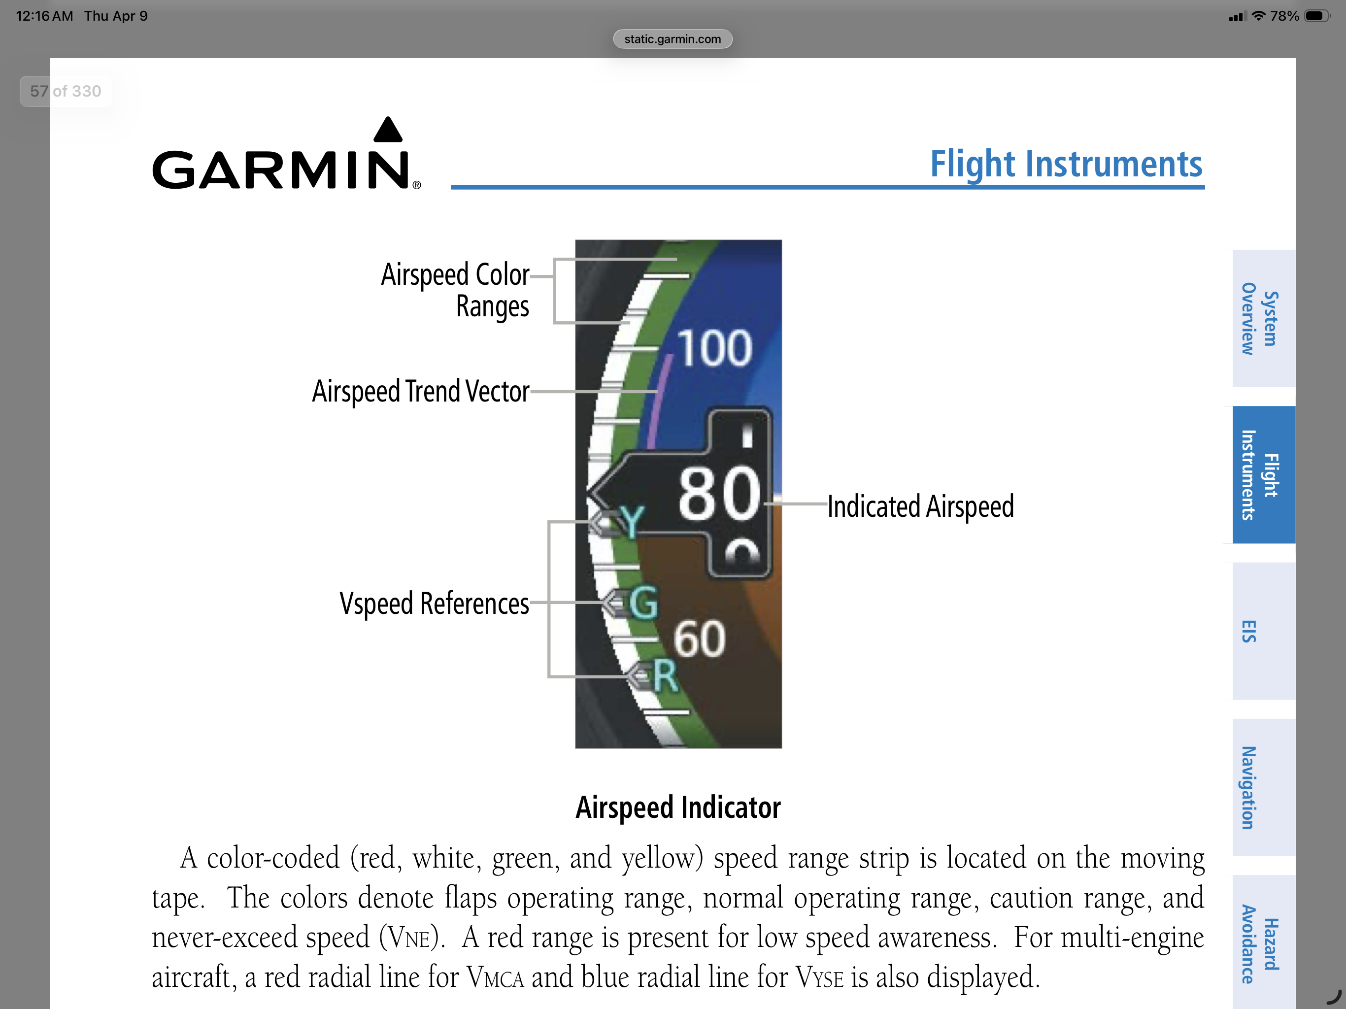
Docs/IMG_0259.png
