HBDrew/PFD-and-AHRS/Docs/IMG_0260.png

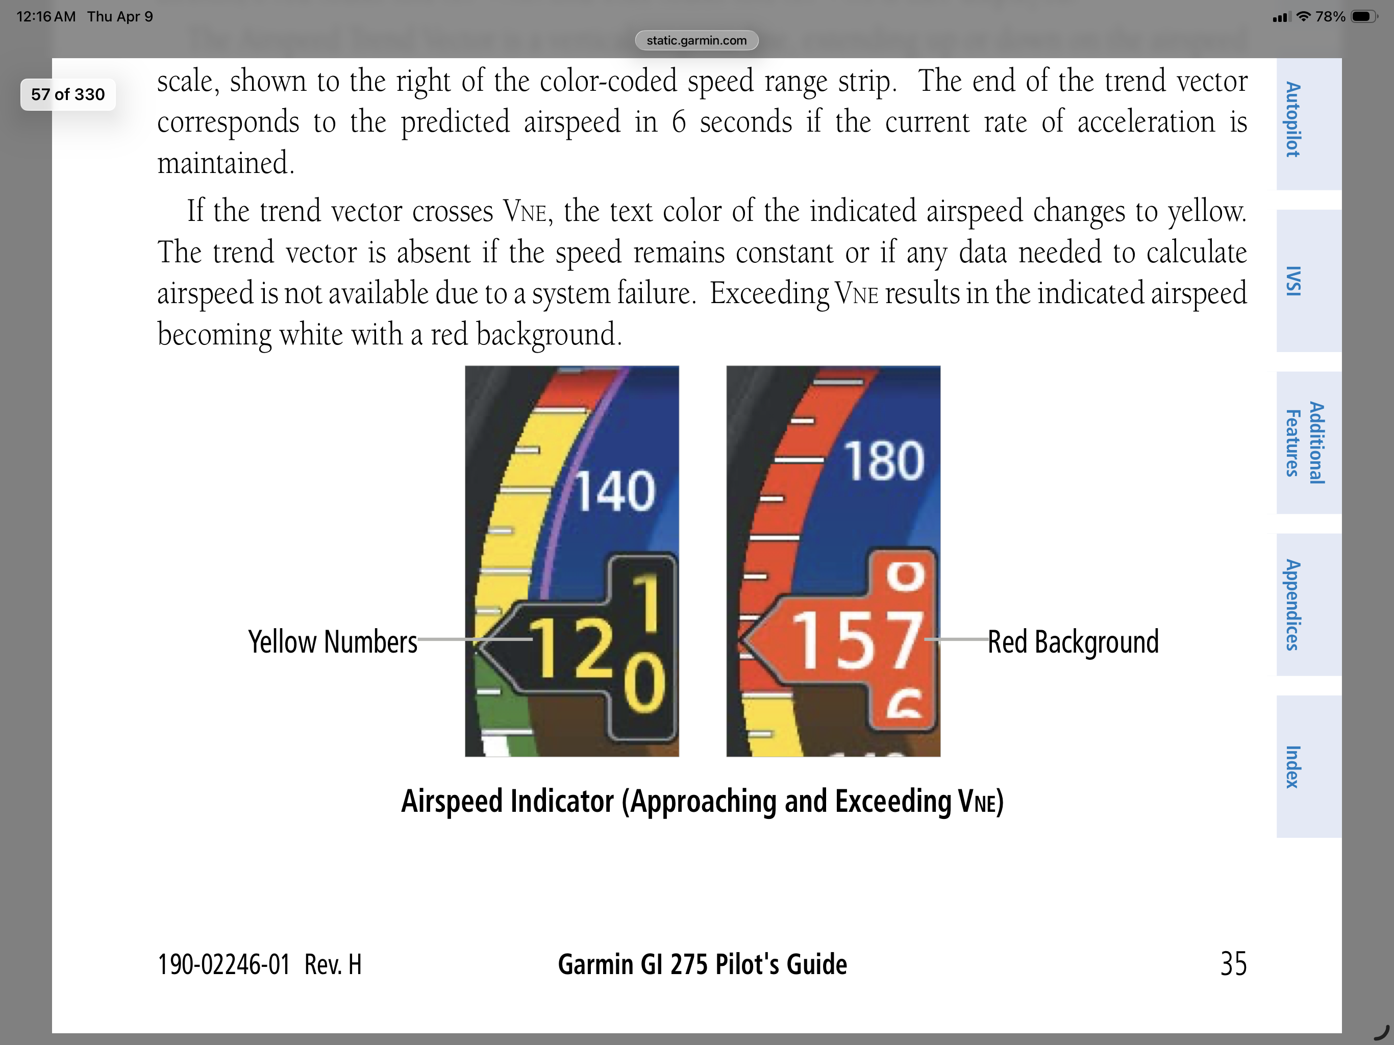
Docs/IMG_0260.png
