HBDrew/PFD-and-AHRS/Docs/IMG_0261.png

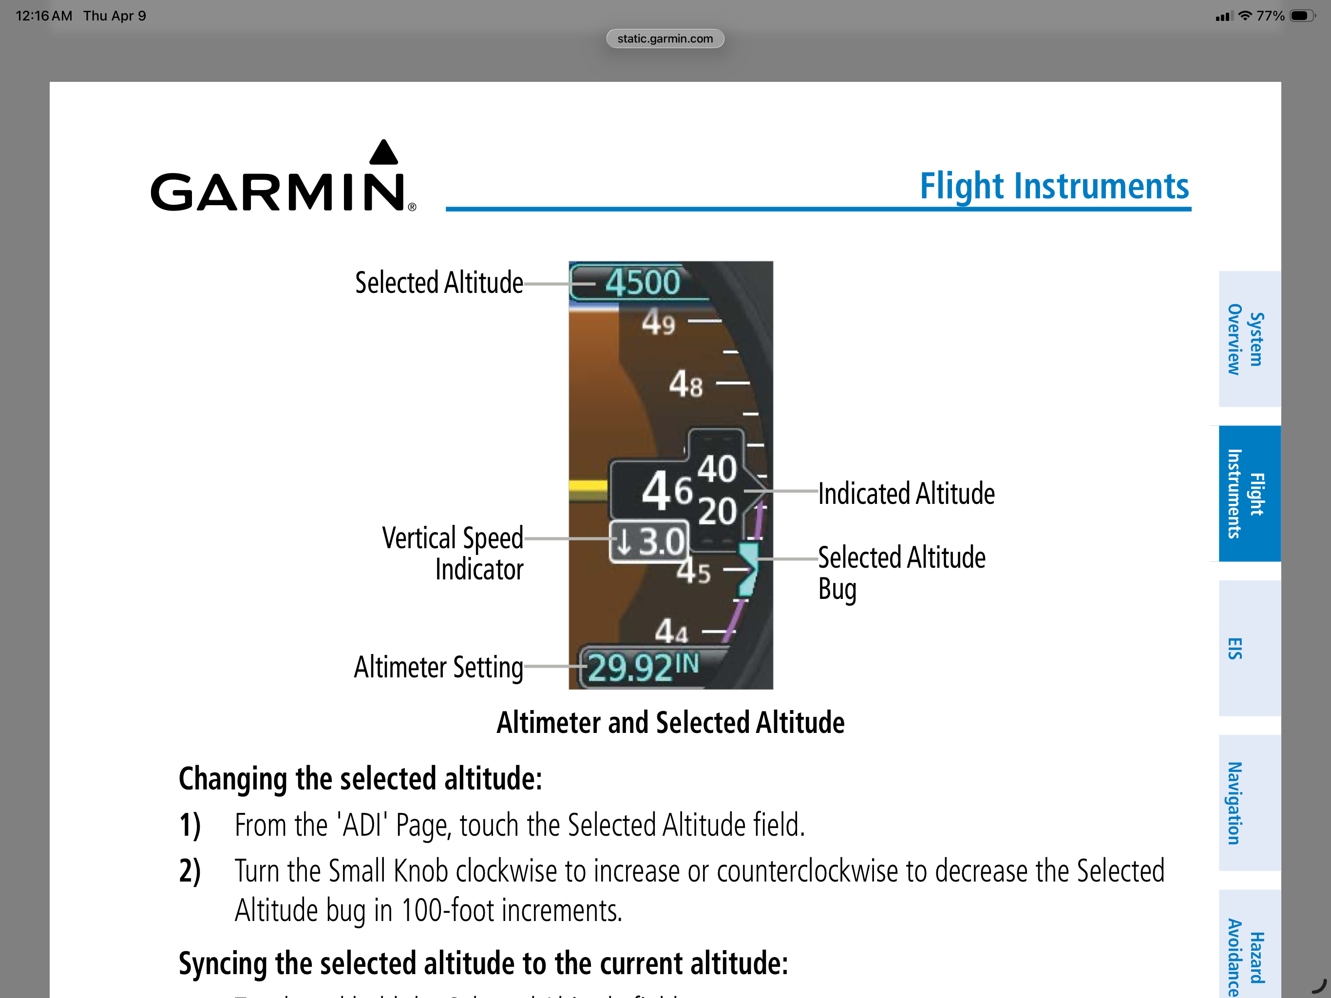
Docs/IMG_0261.png
