HBDrew/PFD-and-AHRS/Docs/IMG_0262.png

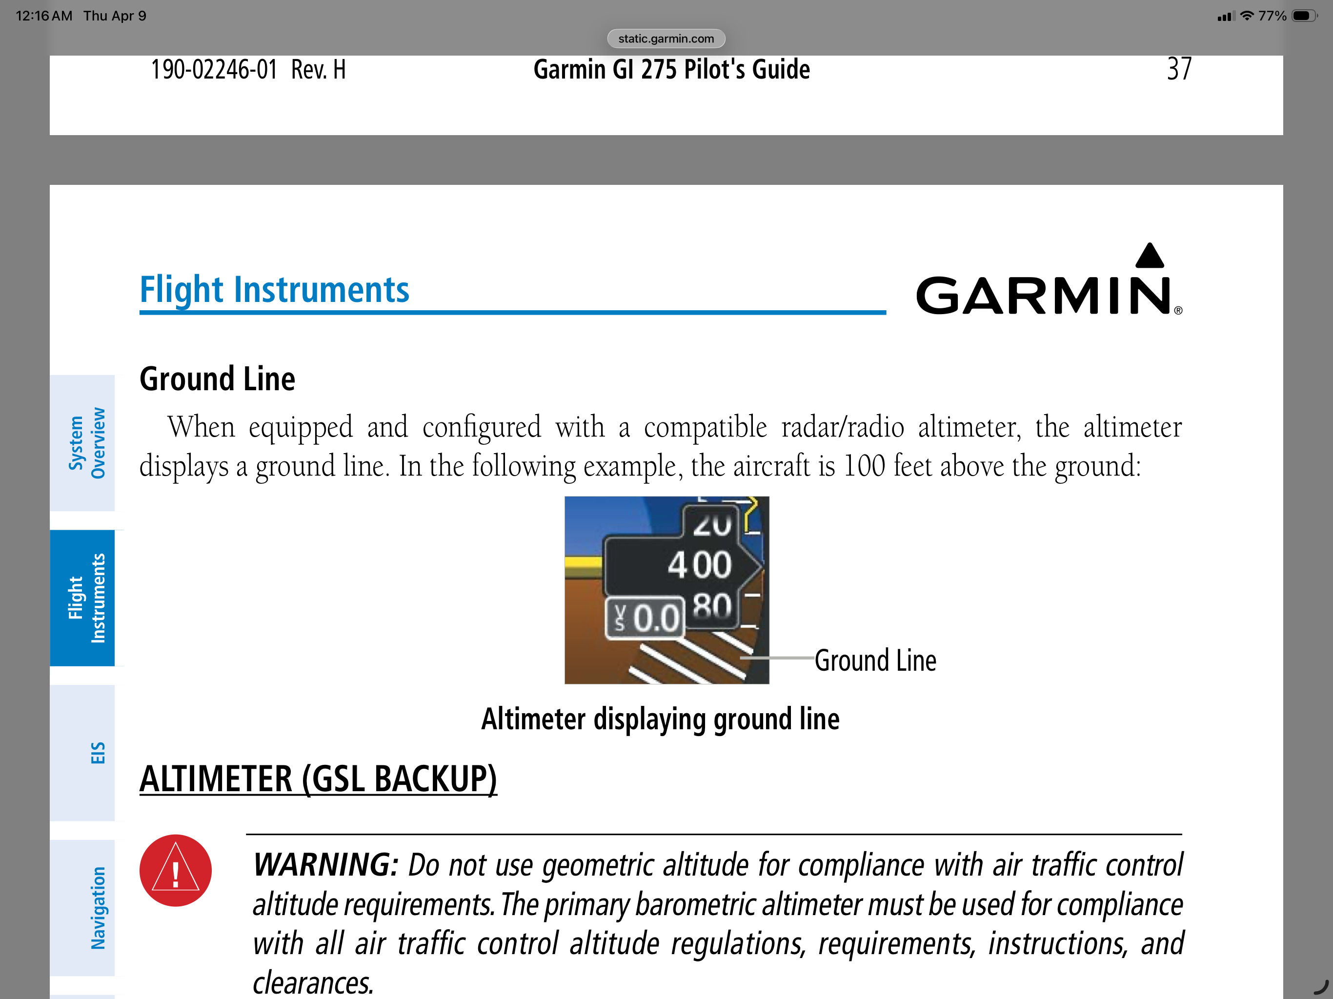
Docs/IMG_0262.png
