HBDrew/PFD-and-AHRS/Docs/IMG_0263.png

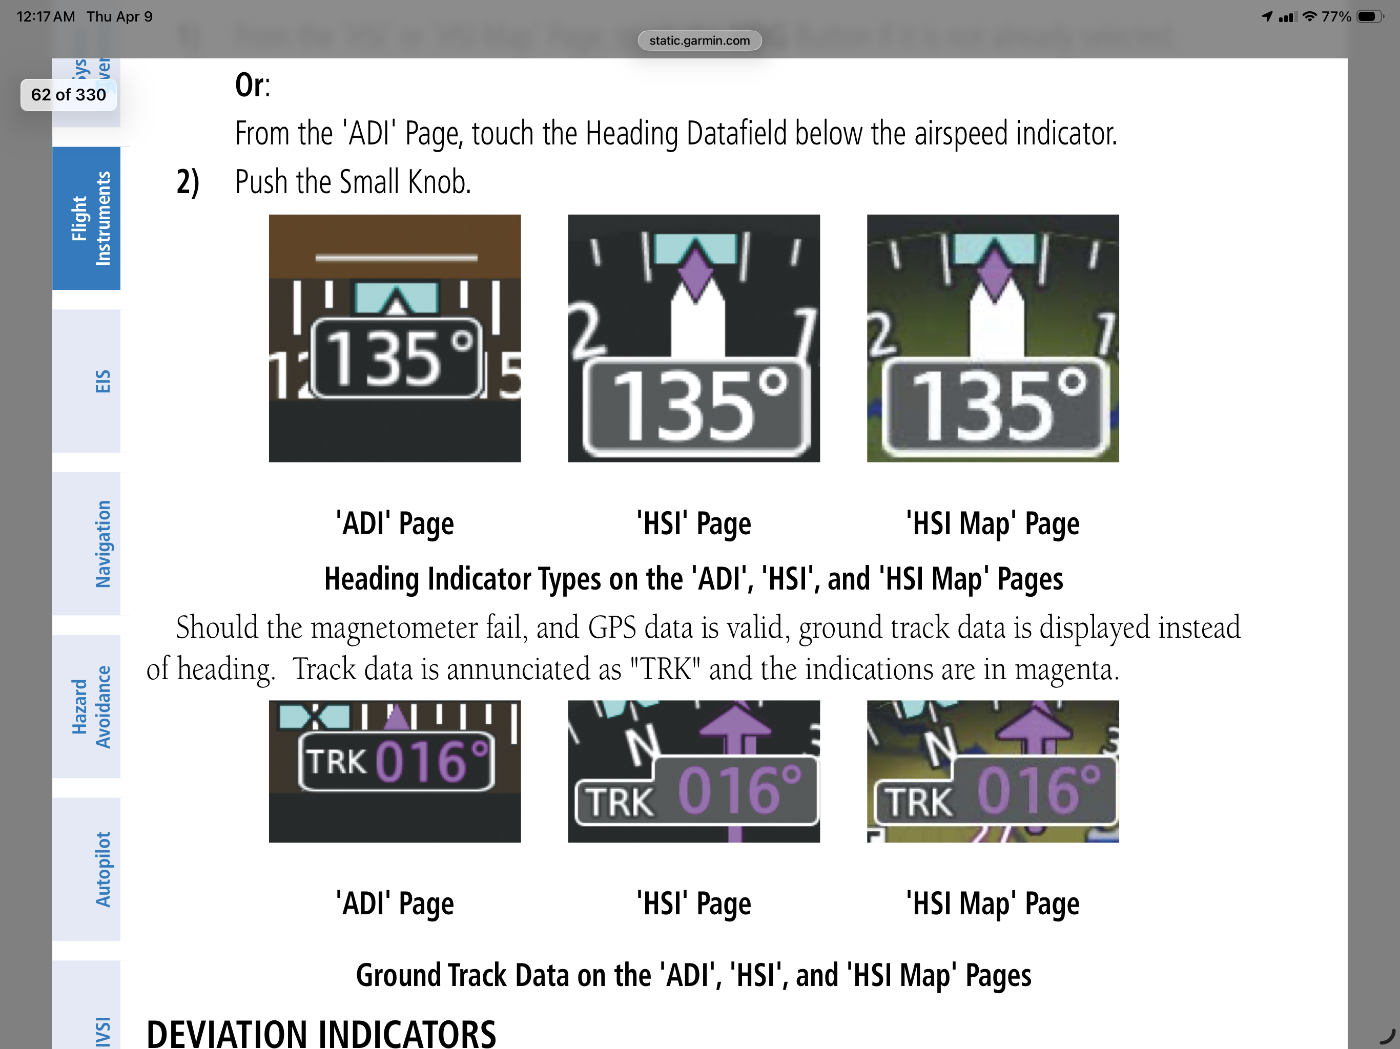
Docs/IMG_0263.png
