HBDrew/PFD-and-AHRS/Docs/IMG_0264.png

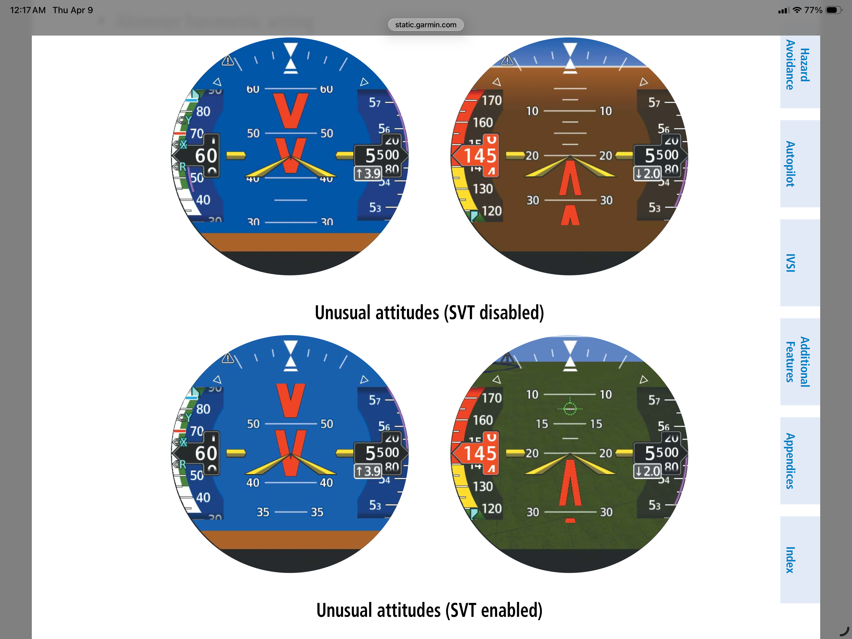
Docs/IMG_0264.png
