HBDrew/PFD-and-AHRS/Docs/IMG_0265.png

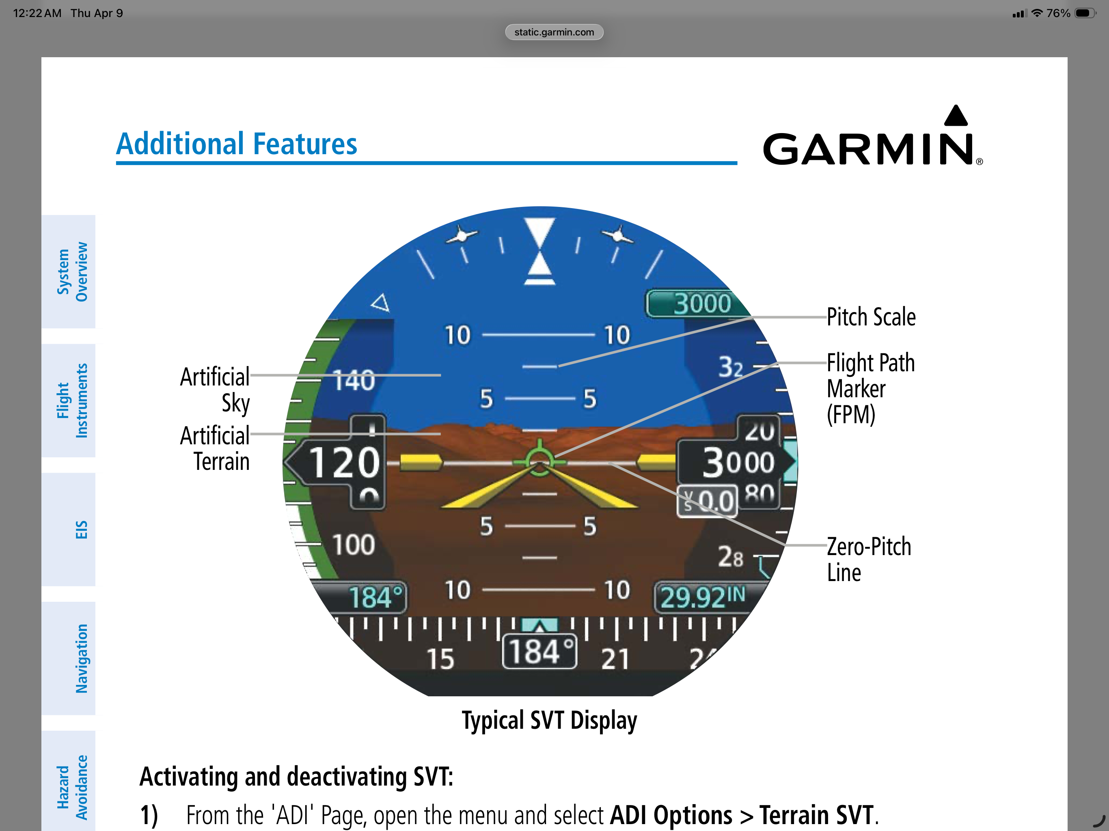
Docs/IMG_0265.png
