HBDrew/PFD-and-AHRS/Docs/IMG_0266.png

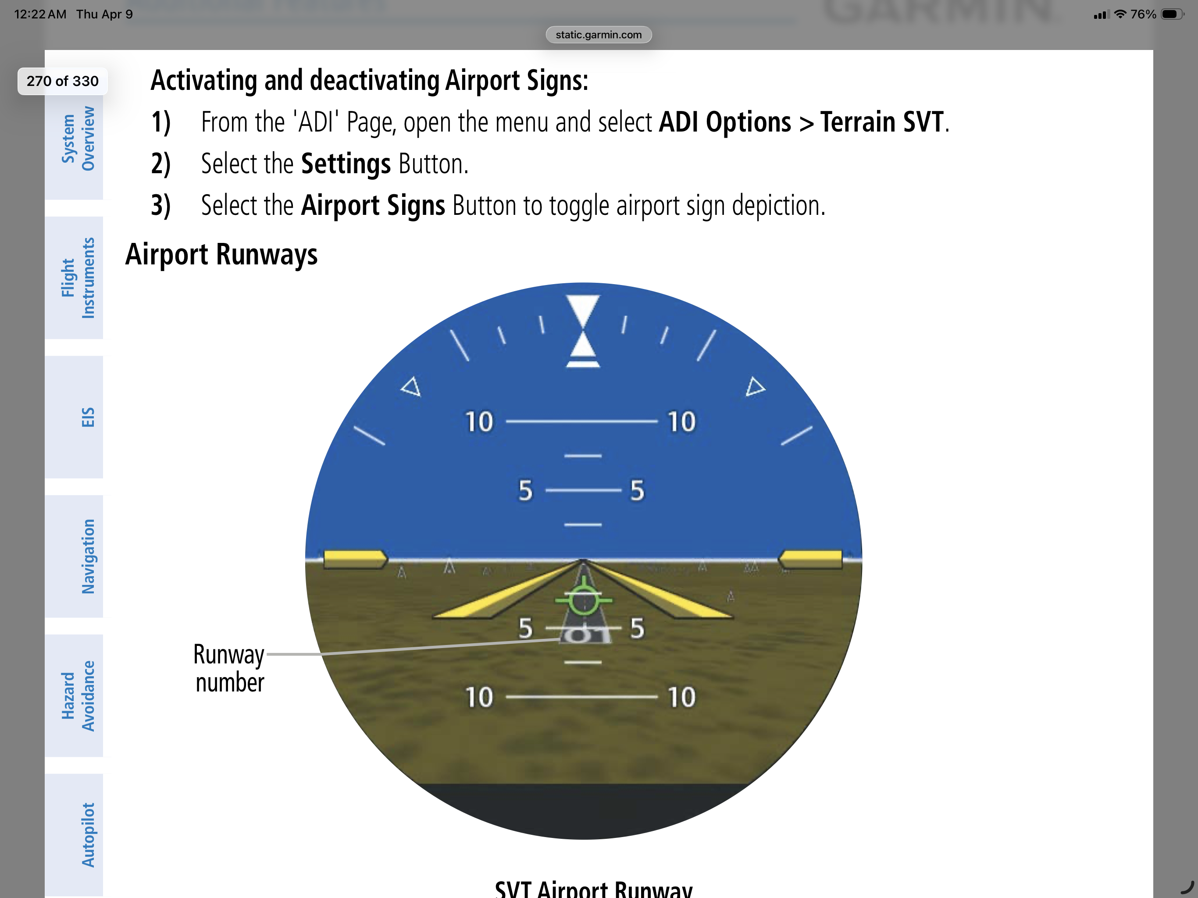
Docs/IMG_0266.png
