HBDrew/PFD-and-AHRS/Docs/IMG_0267.png

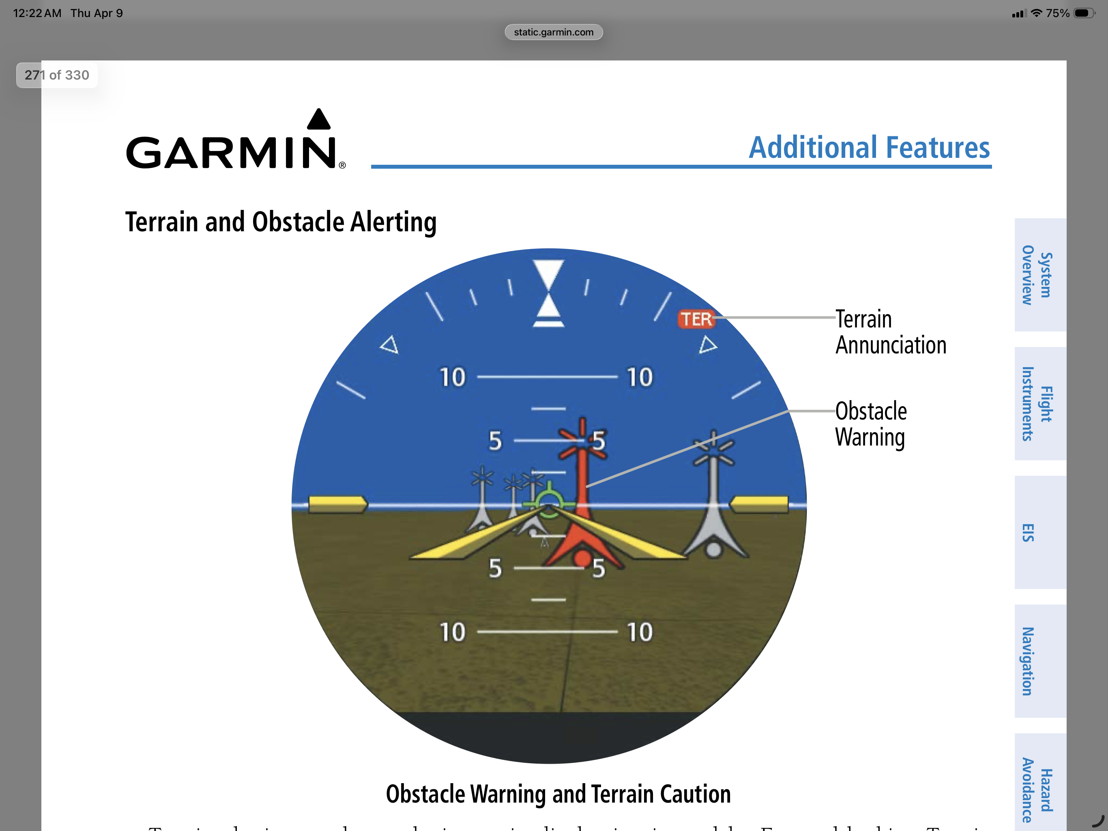
Docs/IMG_0267.png
