HBDrew/PFD-and-AHRS/Docs/IMG_0268.png

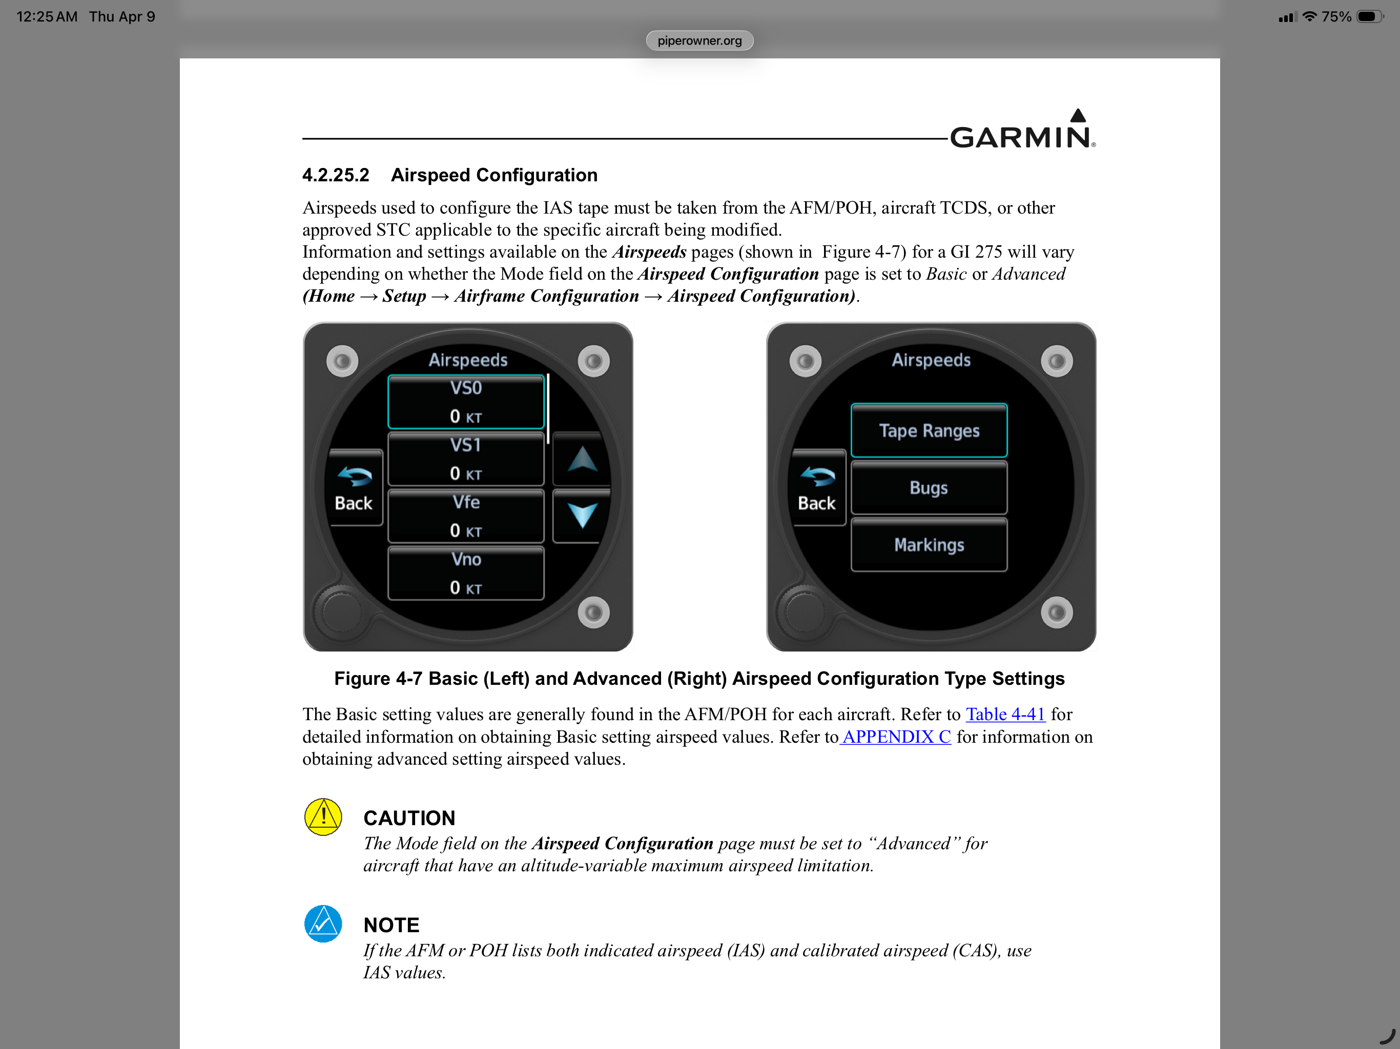
Docs/IMG_0268.png
