HBDrew/PFD-and-AHRS/Docs/IMG_0550.jpeg

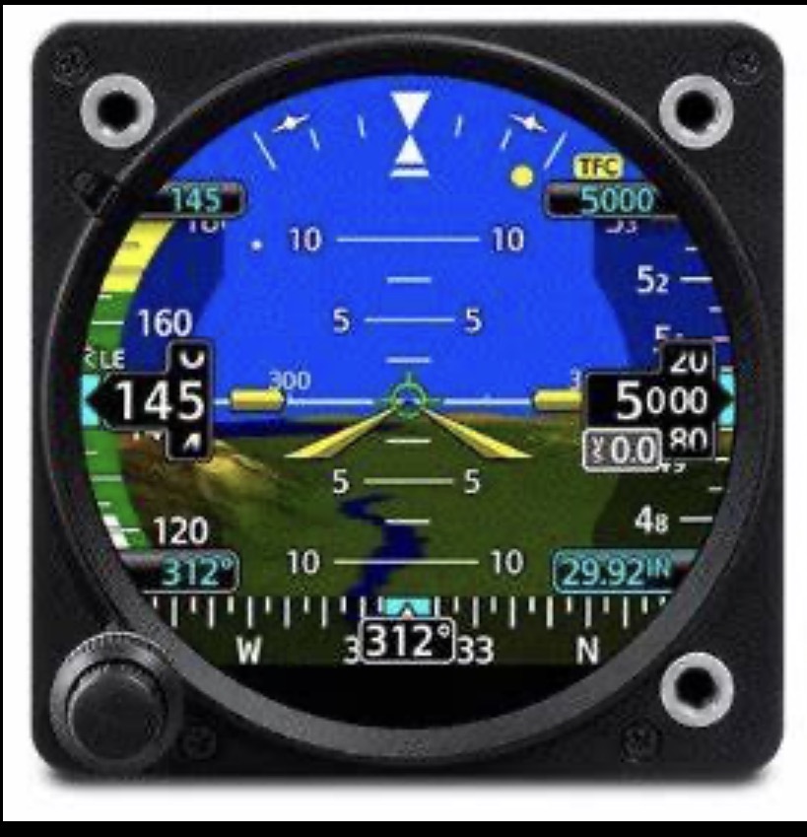
Docs/IMG_0550.jpeg
