HBDrew/PFD-and-AHRS/hardware/v1/enclosure/preview_front.png

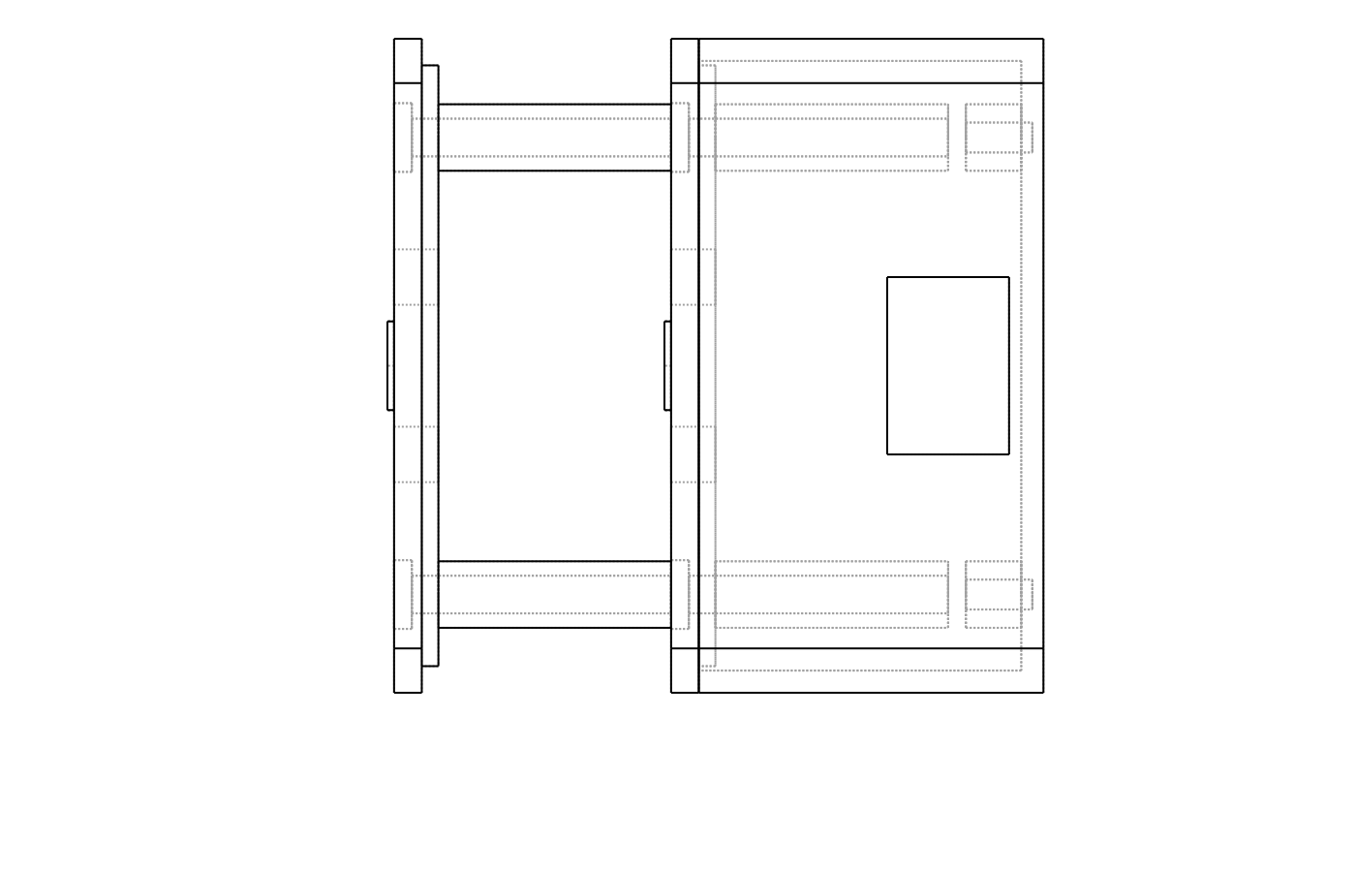
hardware/v1/enclosure/preview_front.png
