HBDrew/PFD-and-AHRS/hardware/v1/enclosure/preview_section.png

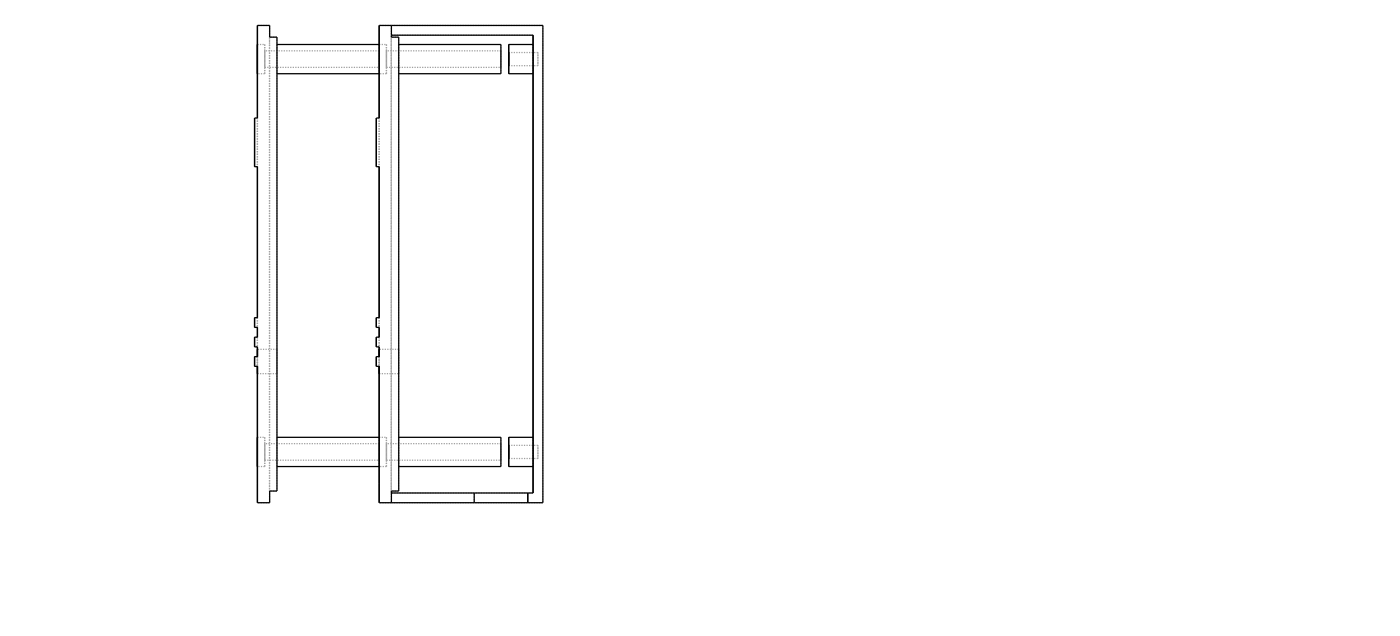
hardware/v1/enclosure/preview_section.png
