HBDrew/PFD-and-AHRS/hardware/v1/enclosure/preview_side.png

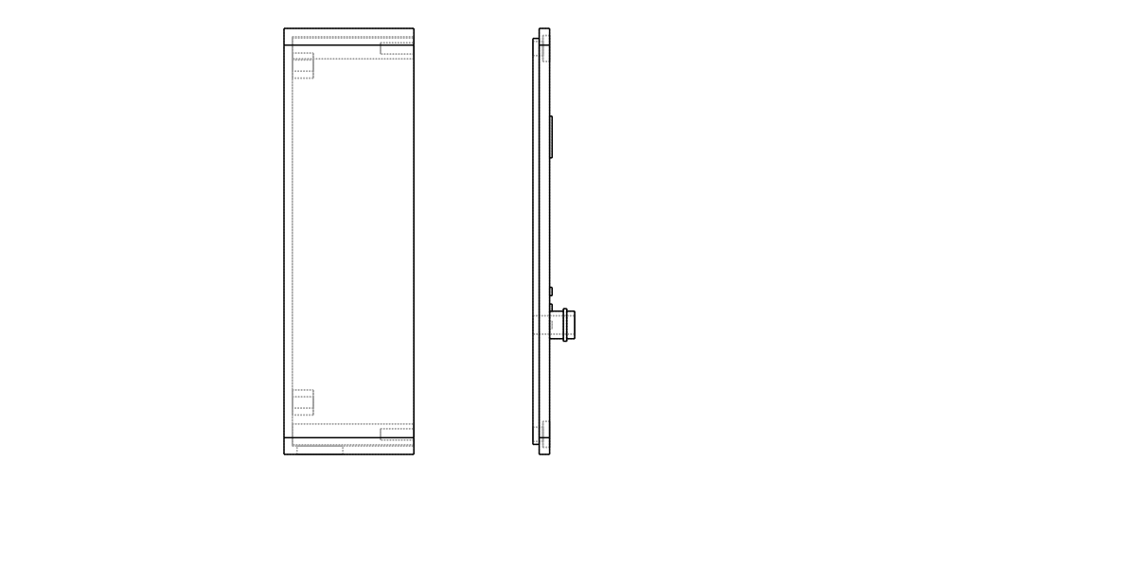
hardware/v1/enclosure/preview_side.png
