HBDrew/PFD-and-AHRS/hardware/v1/enclosure/preview_top.png

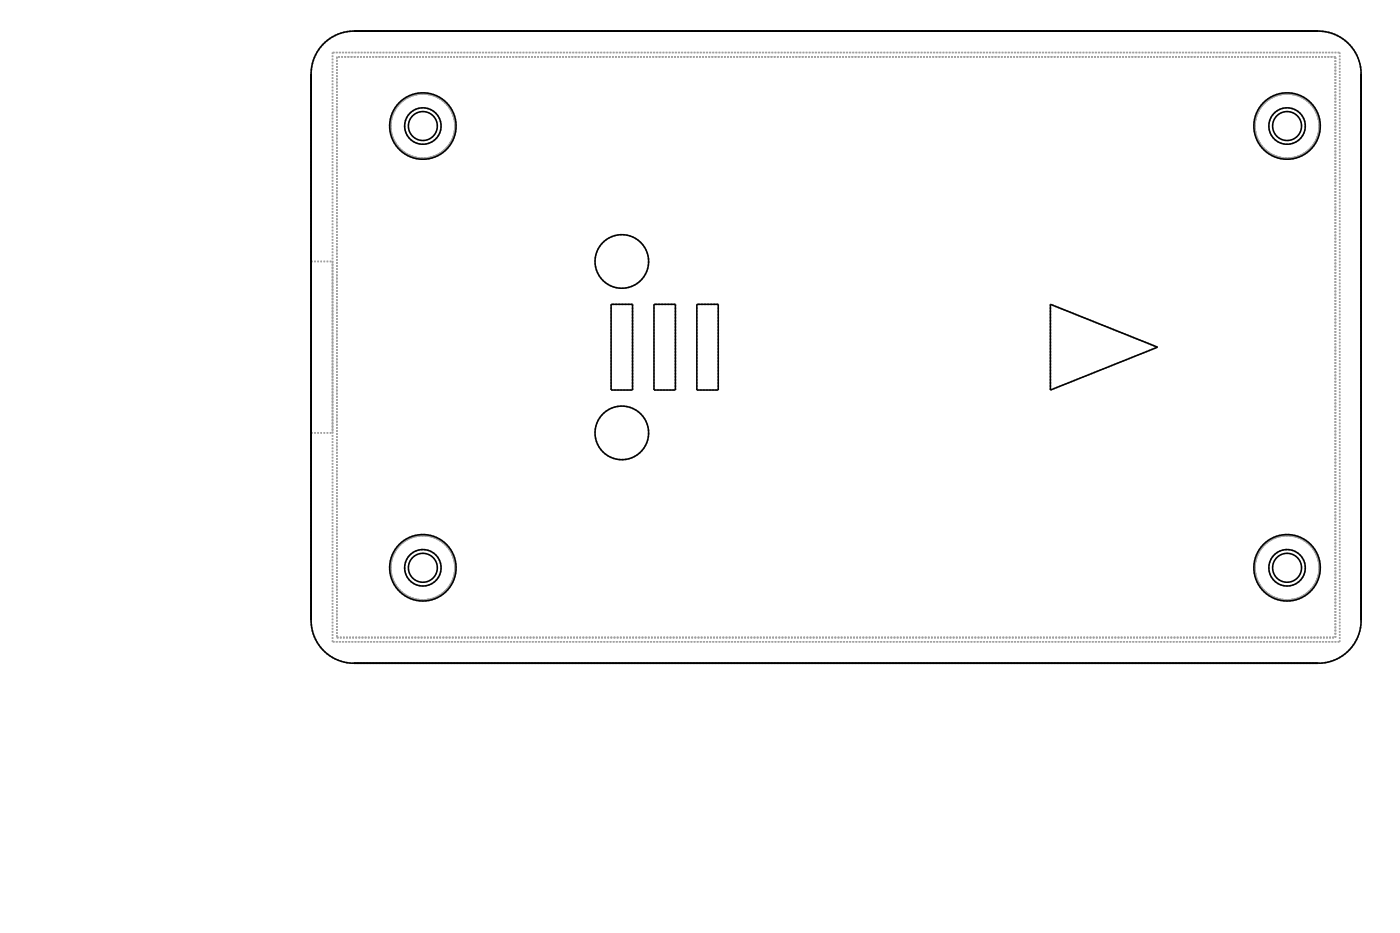
hardware/v1/enclosure/preview_top.png
