HBDrew/PFD-and-AHRS/pfd_preview.png

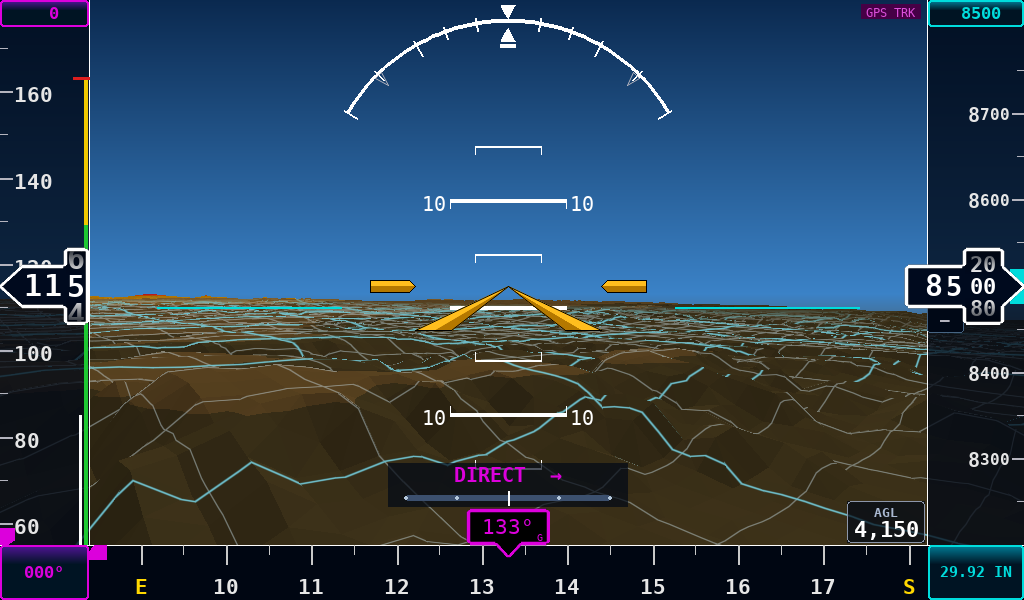
pfd_preview.png
