HBDrew/PFD-and-AHRS/pi4/previews/pfd_gl/preview_climb_left.png

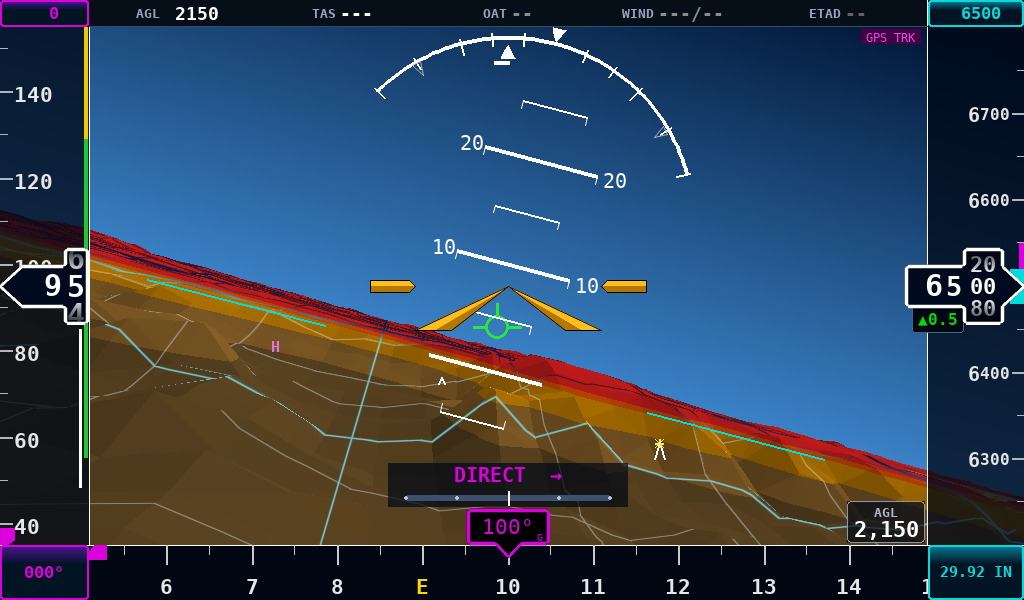
pi4/previews/pfd_gl/preview_climb_left.png
