HBDrew/PFD-and-AHRS/pi4/previews/pfd_gl/preview_direct_to_ksez.png

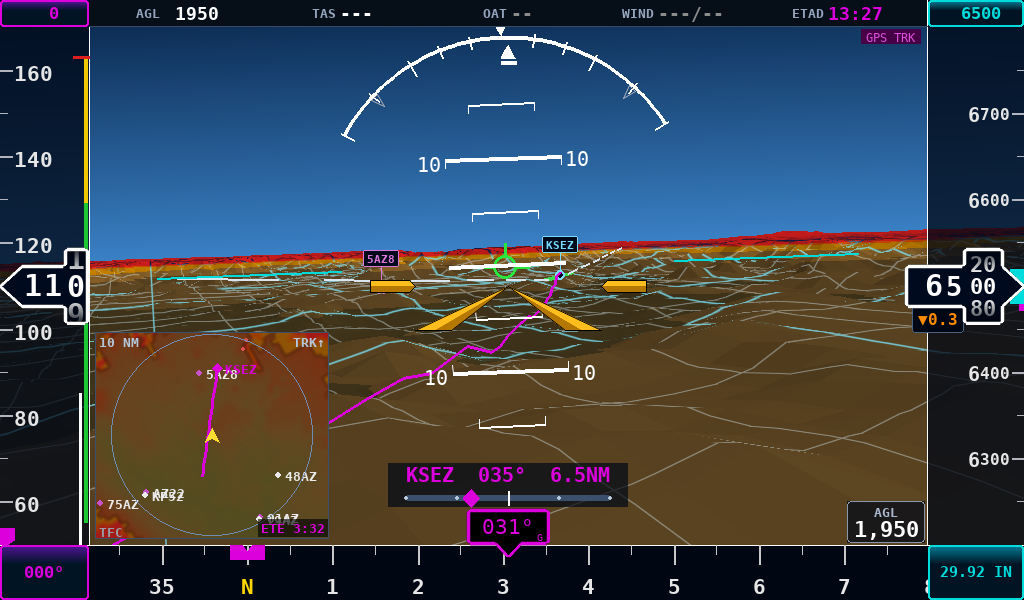
pi4/previews/pfd_gl/preview_direct_to_ksez.png
