HBDrew/PFD-and-AHRS/pi4/previews/pfd_gl/preview_high_altitude.png

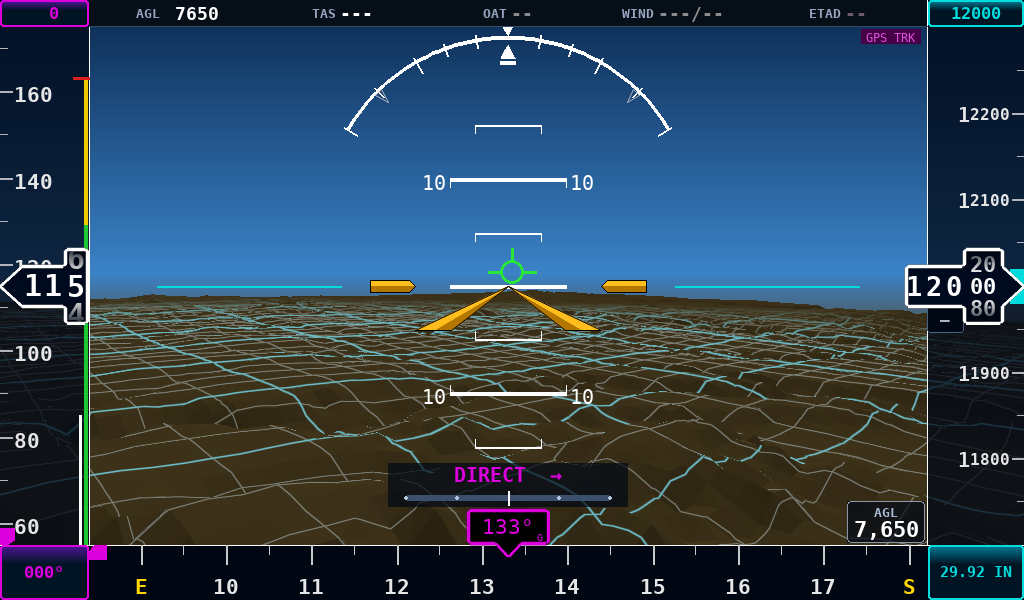
pi4/previews/pfd_gl/preview_high_altitude.png
