HBDrew/PFD-and-AHRS/pi4/previews/pfd_gl/preview_low_altitude.png

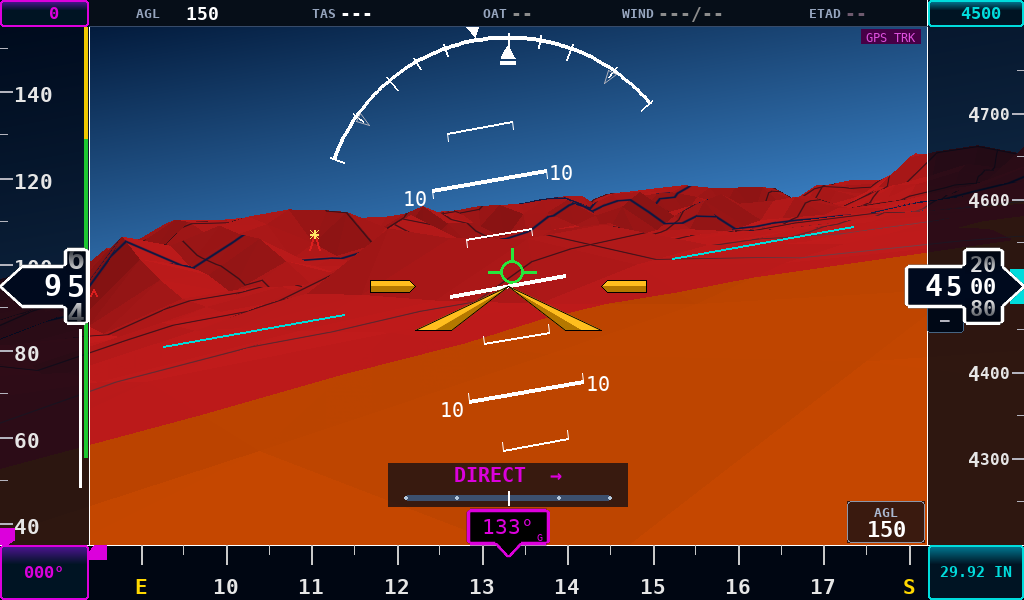
pi4/previews/pfd_gl/preview_low_altitude.png
