HBDrew/PFD-and-AHRS/pi4/previews/pfd_gl/preview_synthetic_approach.png

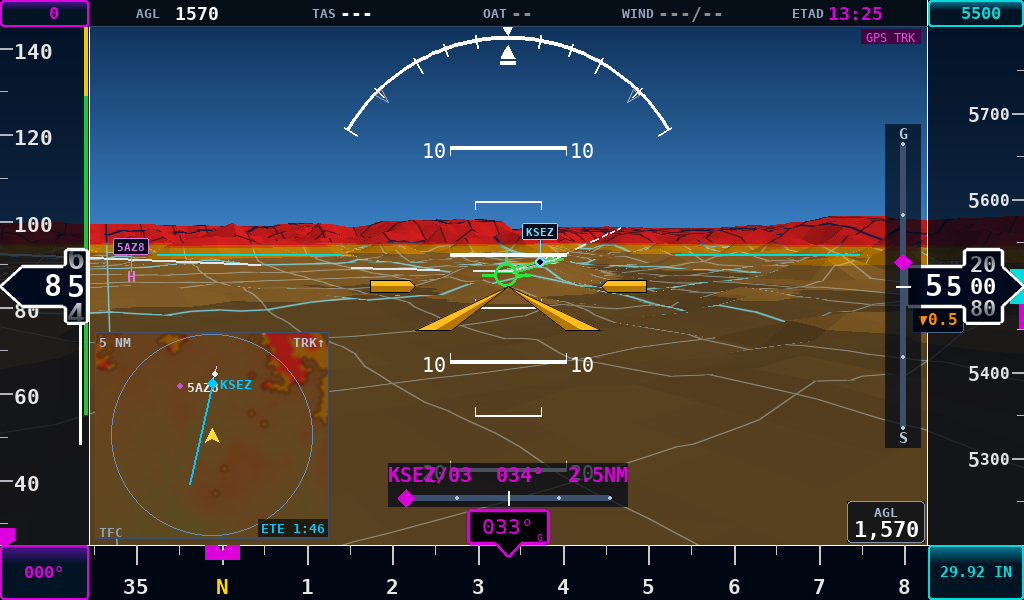
pi4/previews/pfd_gl/preview_synthetic_approach.png
