HBDrew/PFD-and-AHRS/pi4/previews/pfd_preview.png

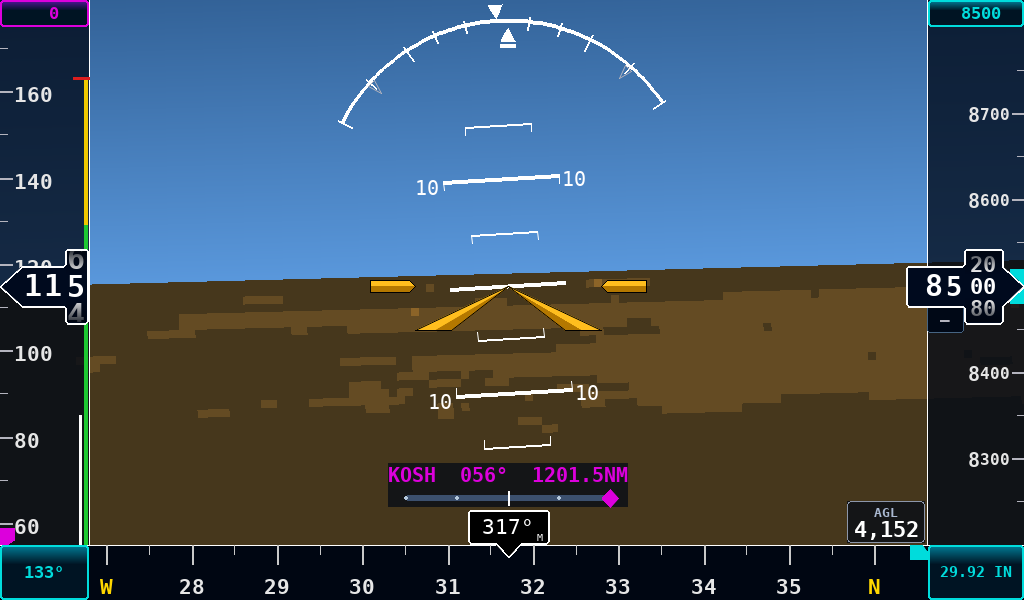
pi4/previews/pfd_preview.png
