HBDrew/PFD-and-AHRS/pi4/previews/preview_airport_idle.png

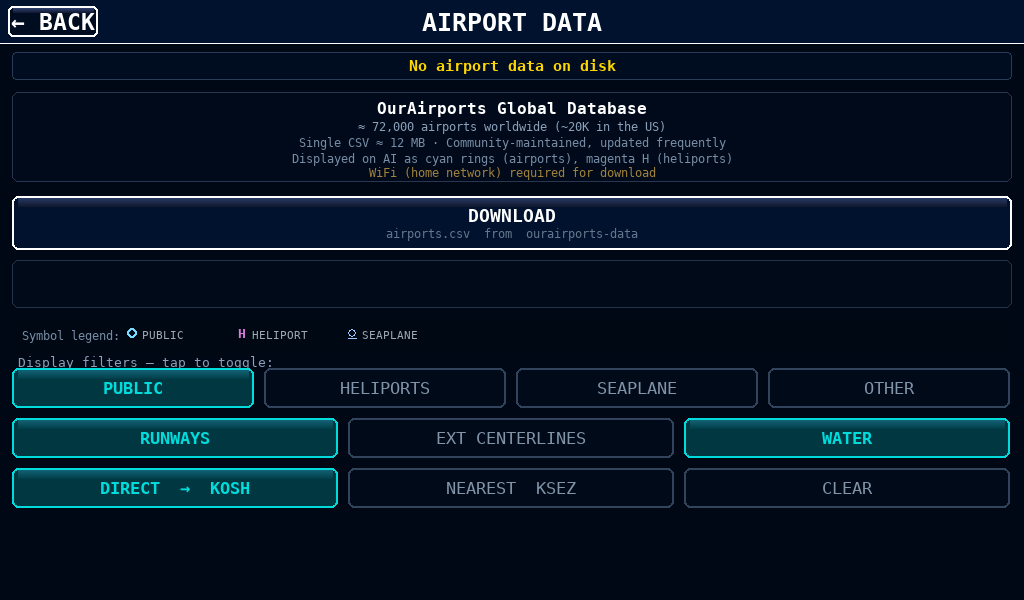
pi4/previews/preview_airport_idle.png
