HBDrew/PFD-and-AHRS/pi4/previews/preview_compass_cal_done.png

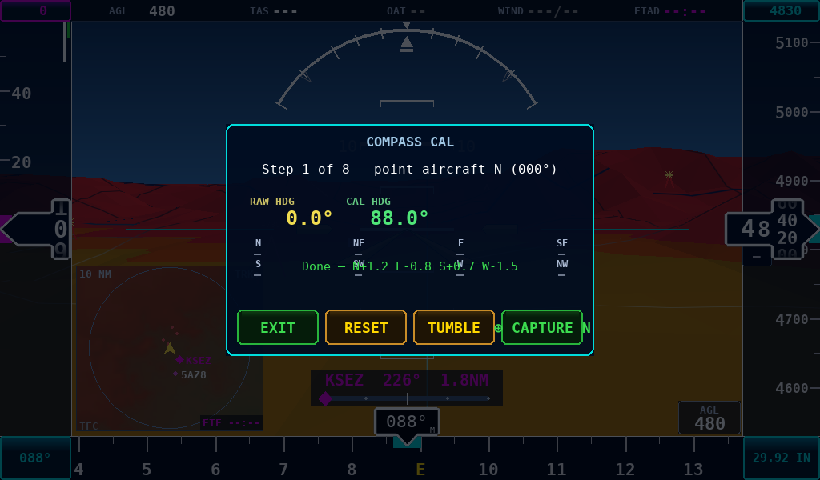
pi4/previews/preview_compass_cal_done.png
