HBDrew/PFD-and-AHRS/pi4/previews/preview_gps_trk_mode.png

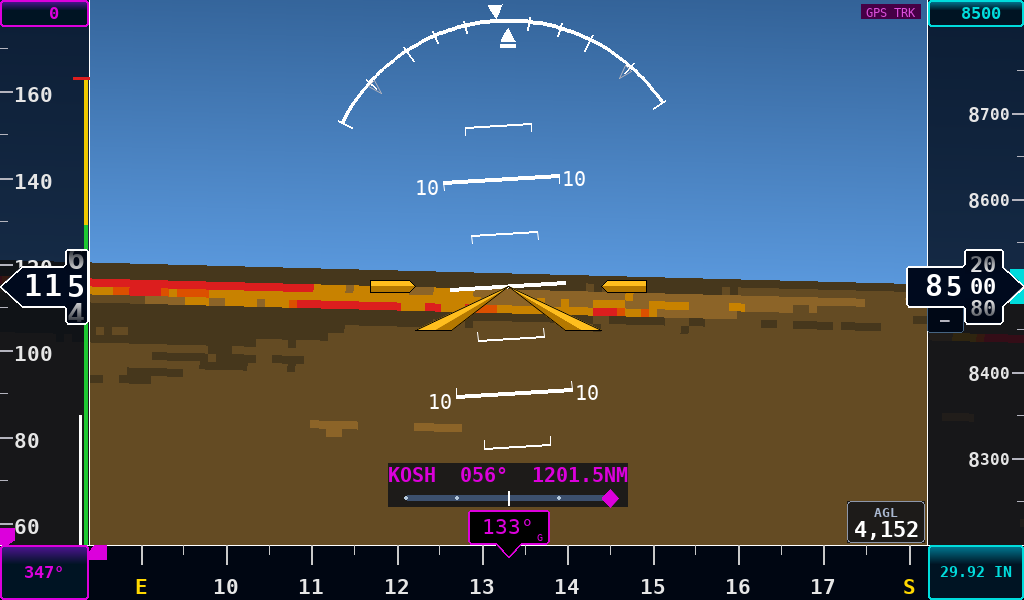
pi4/previews/preview_gps_trk_mode.png
