HBDrew/PFD-and-AHRS/pi4/previews/preview_numpad_hdg.png

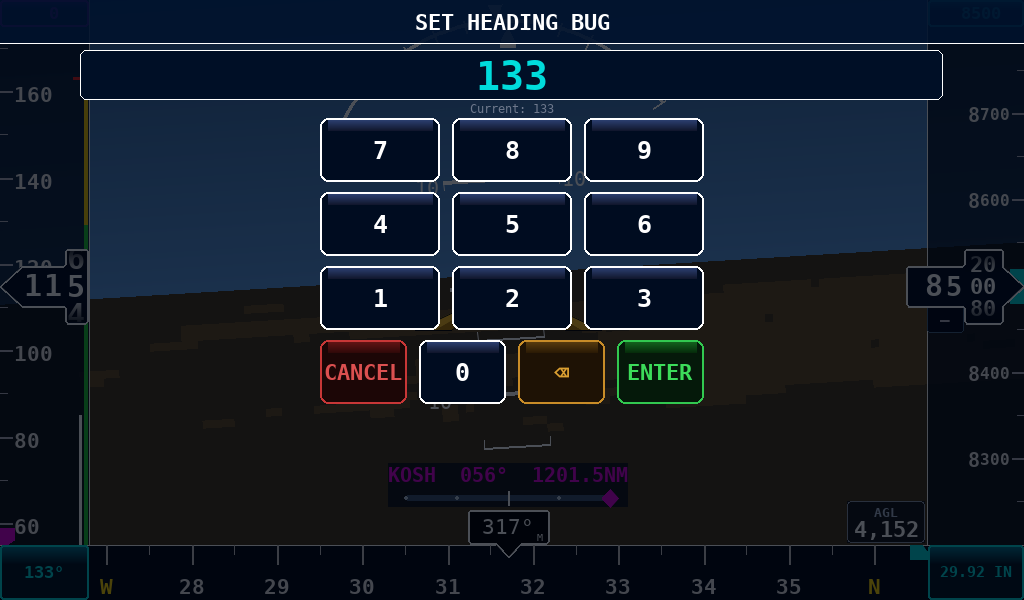
pi4/previews/preview_numpad_hdg.png
