HBDrew/PFD-and-AHRS/pi4/previews/preview_obstacle_downloading.png

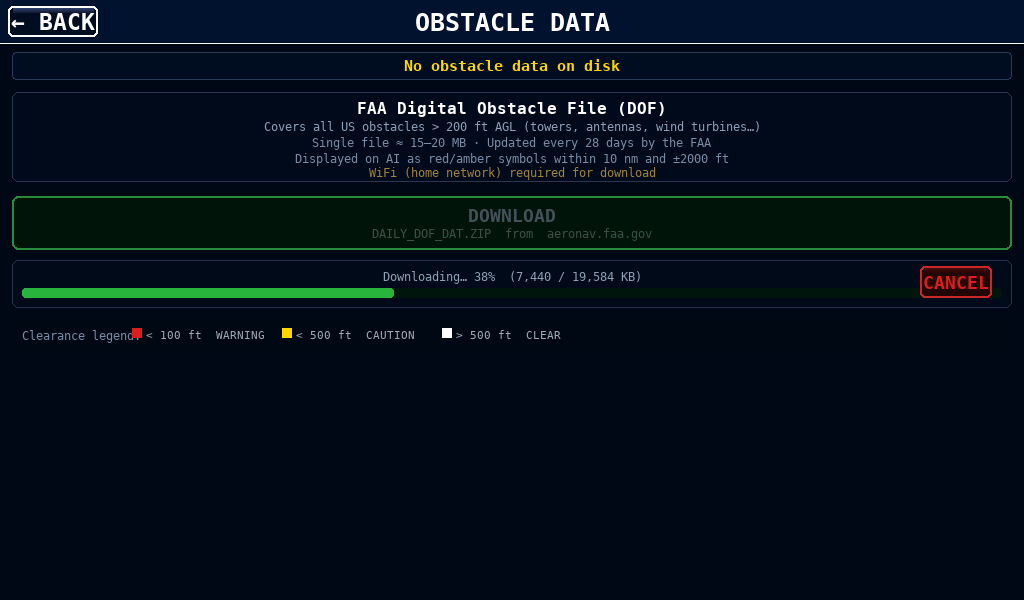
pi4/previews/preview_obstacle_downloading.png
