HBDrew/PFD-and-AHRS/pi4/previews/preview_obstacle_loaded.png

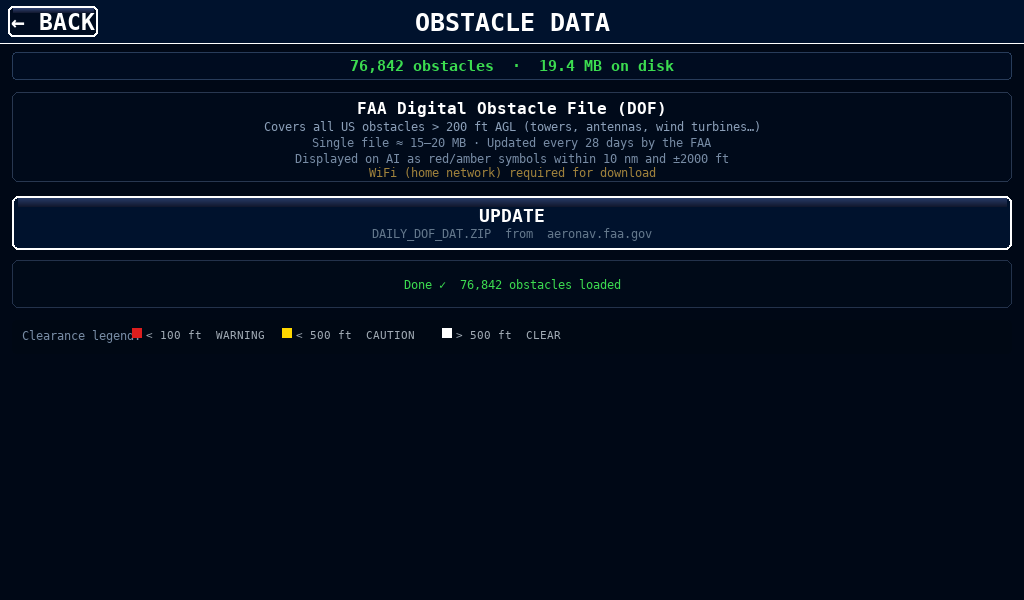
pi4/previews/preview_obstacle_loaded.png
