HBDrew/PFD-and-AHRS/pi4/previews/preview_sedona_climb_turn.png

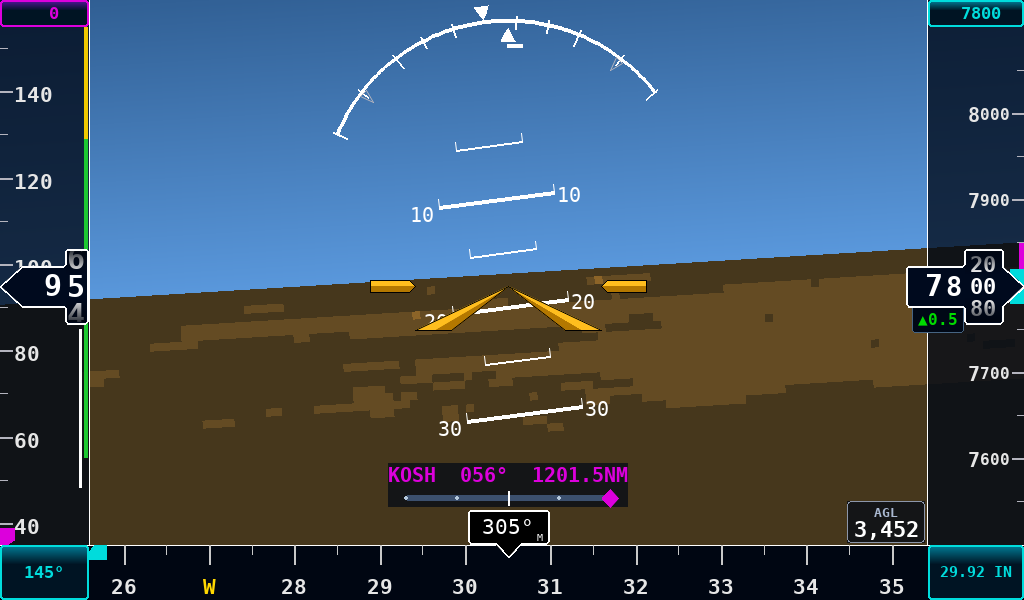
pi4/previews/preview_sedona_climb_turn.png
