HBDrew/PFD-and-AHRS/pi4/previews/preview_sedona_level.png

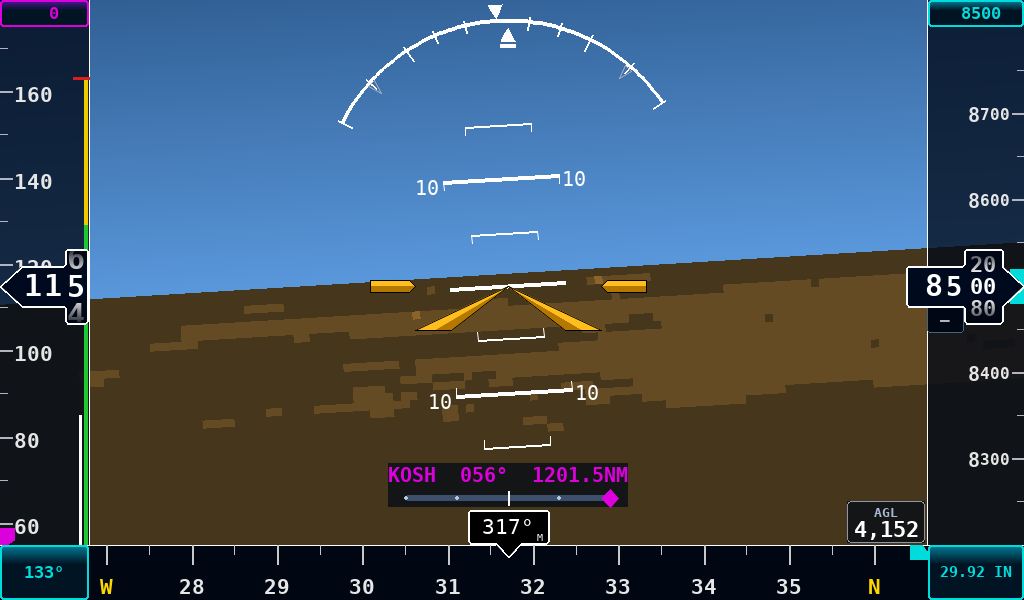
pi4/previews/preview_sedona_level.png
