HBDrew/PFD-and-AHRS/pi4/previews/preview_terrain_caution.png

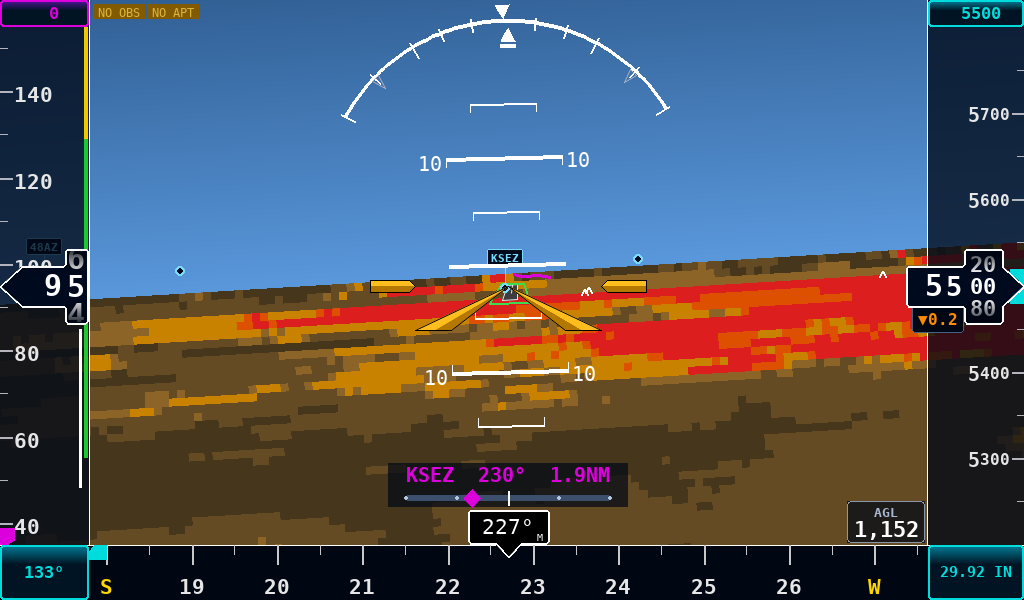
pi4/previews/preview_terrain_caution.png
