HBDrew/PFD-and-AHRS/pi4/previews/preview_terrain_warning.png

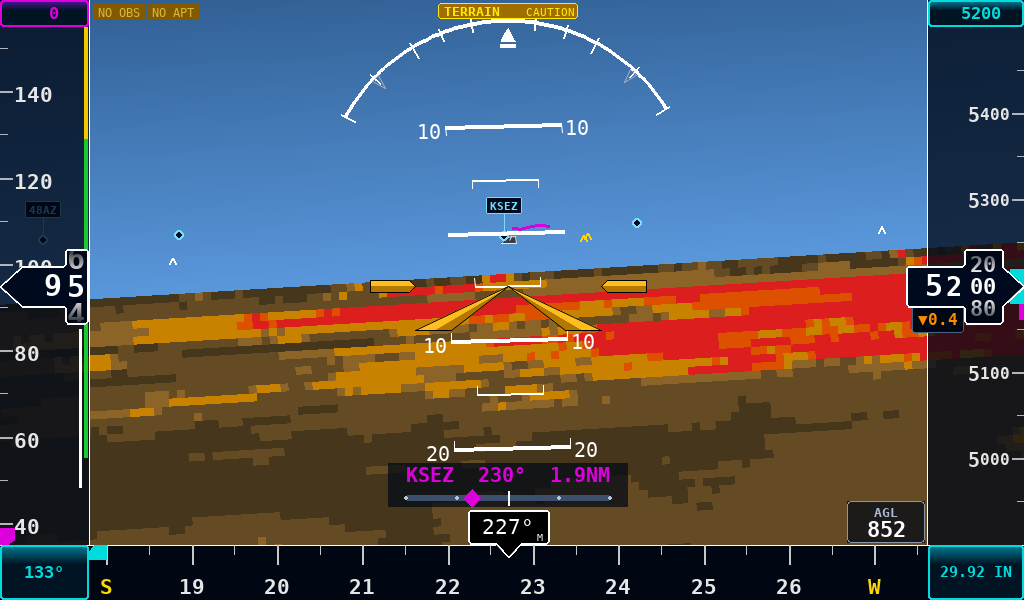
pi4/previews/preview_terrain_warning.png
