HBDrew/PFD-and-AHRS/pi4/previews/preview_unknown_waypoint.png

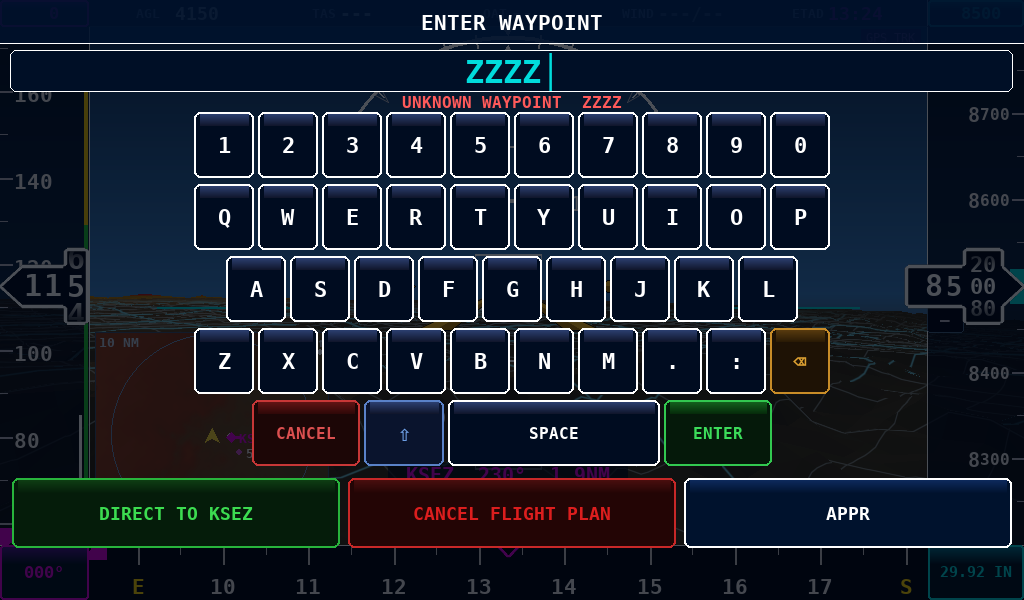
pi4/previews/preview_unknown_waypoint.png
