HBDrew/PFD-and-AHRS/pi_zero/previews/preview_airport_idle.png

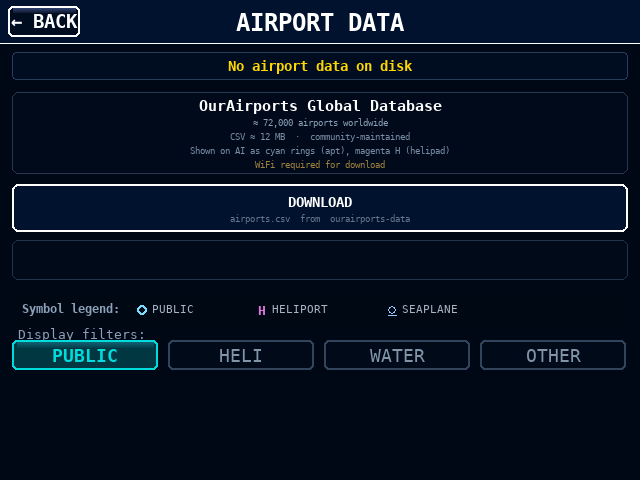
pi_zero/previews/preview_airport_idle.png
