HBDrew/PFD-and-AHRS/pi_zero/previews/preview_numpad_baro_hpa.png

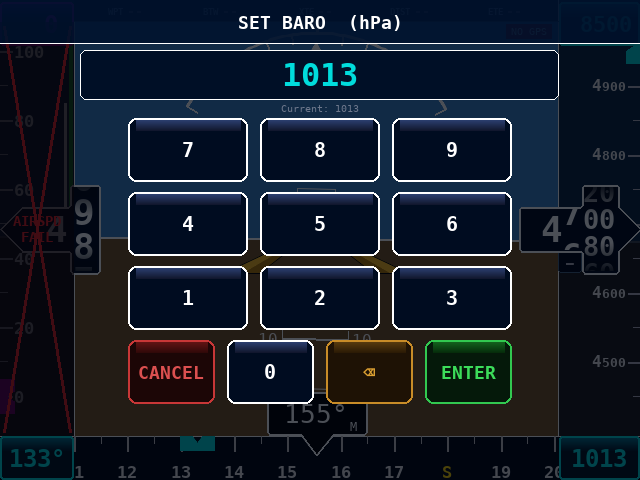
pi_zero/previews/preview_numpad_baro_hpa.png
