HBDrew/PFD-and-AHRS/pi_zero/previews/preview_obstacle_downloading.png

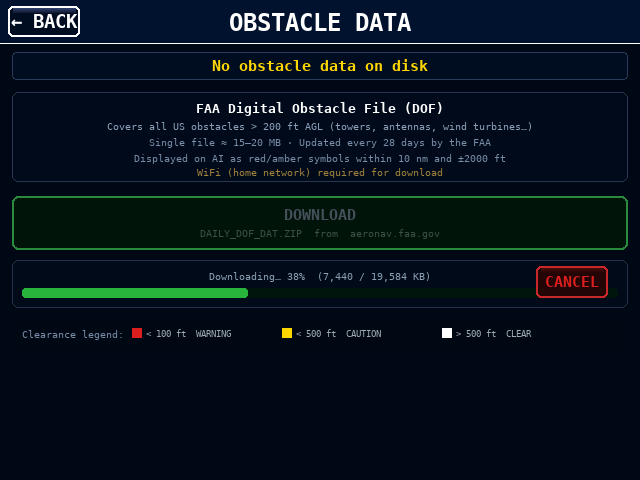
pi_zero/previews/preview_obstacle_downloading.png
