HBDrew/PFD-and-AHRS/pi_zero/previews/preview_obstacle_loaded.png

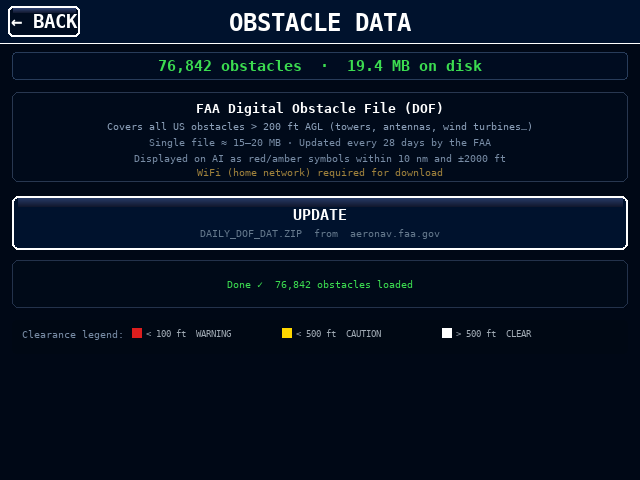
pi_zero/previews/preview_obstacle_loaded.png
