HBDrew/PFD-and-AHRS/pi_zero/previews/preview_terrain_caution.png

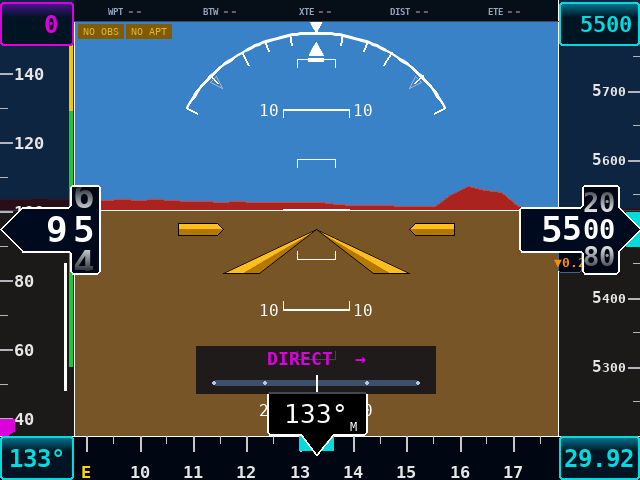
pi_zero/previews/preview_terrain_caution.png
