HBDrew/PFD-and-AHRS/pi_zero/previews/preview_terrain_warning.png

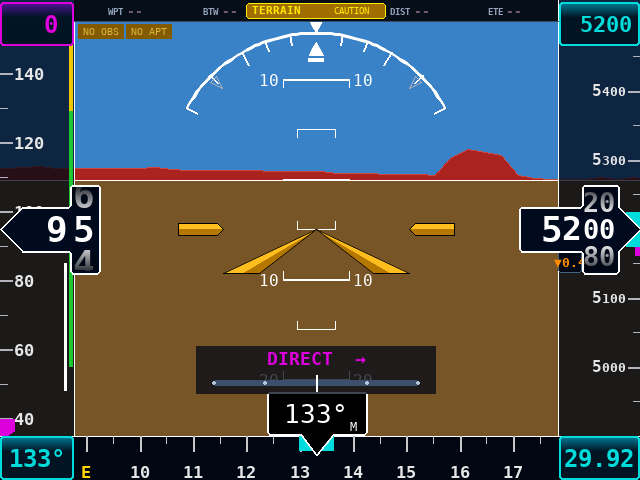
pi_zero/previews/preview_terrain_warning.png
