HBDrew/PFD-and-AHRS/tools/preview_gps_trk_mode.png

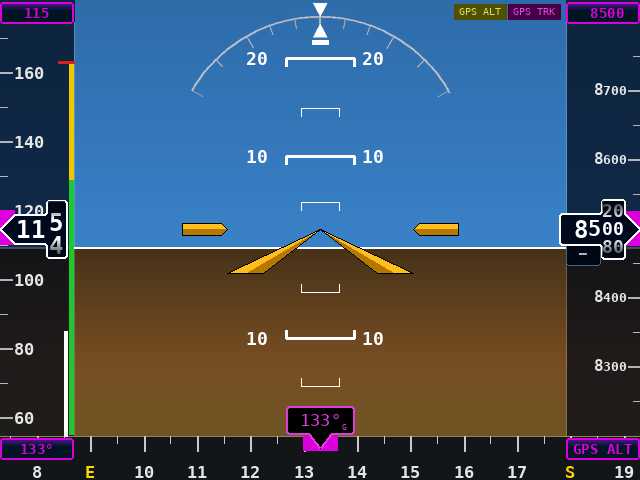
tools/preview_gps_trk_mode.png
