HBDrew/PFD-and-AHRS/tools/preview_keyboard.png

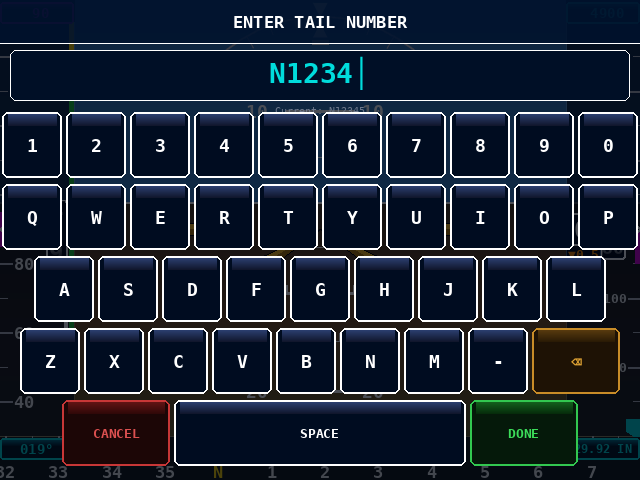
tools/preview_keyboard.png
