HBDrew/PFD-and-AHRS/tools/preview_numpad_alt.png

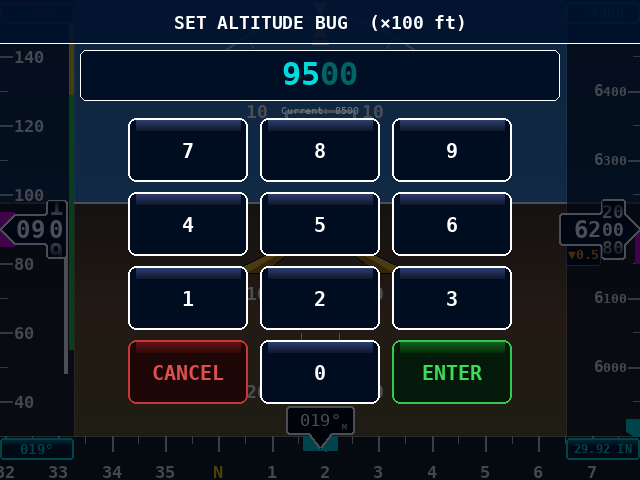
tools/preview_numpad_alt.png
