HBDrew/PFD-and-AHRS/tools/preview_numpad_baro_inhg.png

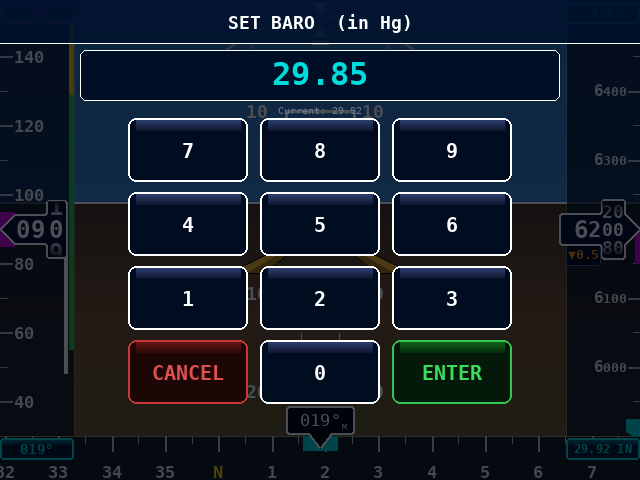
tools/preview_numpad_baro_inhg.png
