HBDrew/PFD-and-AHRS/tools/preview_obstacle_downloading.png

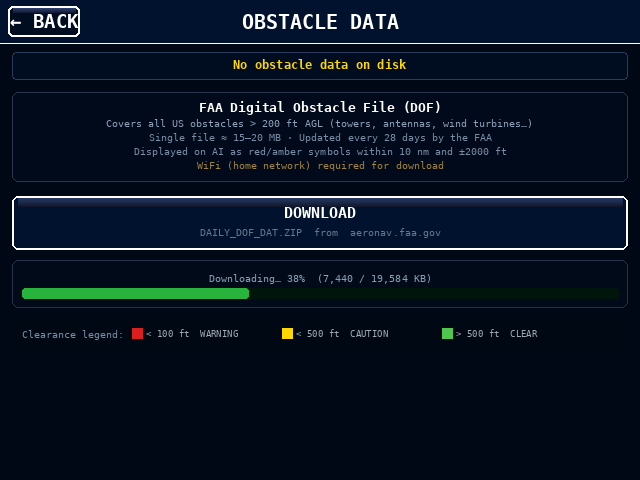
tools/preview_obstacle_downloading.png
