HBDrew/PFD-and-AHRS/tools/preview_sedona_approach.png

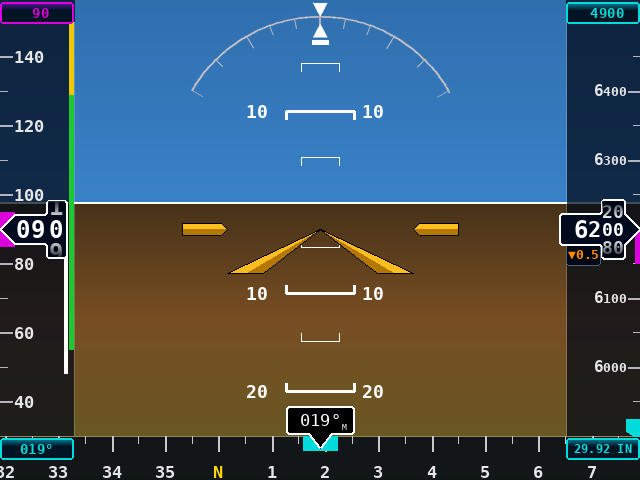
tools/preview_sedona_approach.png
