HBDrew/PFD-and-AHRS/tools/preview_sedona_climb_turn.png

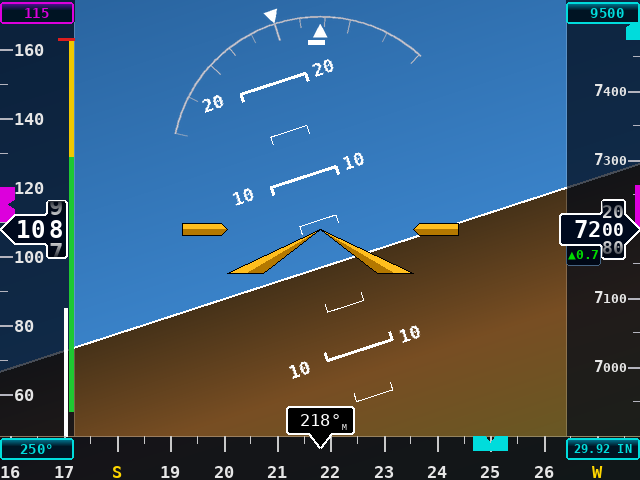
tools/preview_sedona_climb_turn.png
