HBDrew/PFD-and-AHRS/tools/preview_sedona_level.png

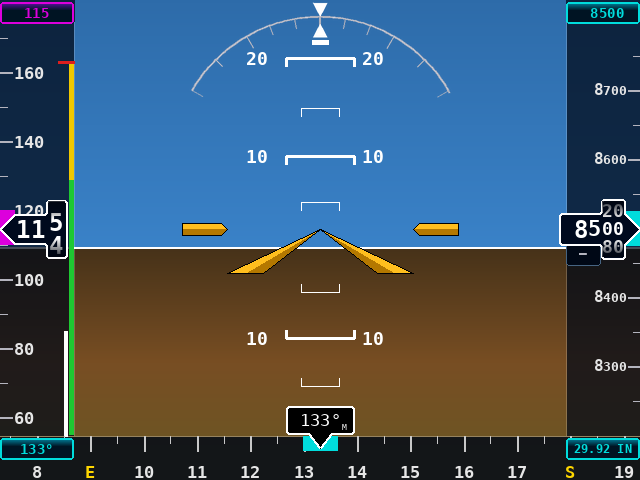
tools/preview_sedona_level.png
