HBDrew/PFD-and-AHRS/tools/preview_terrain_downloading.png

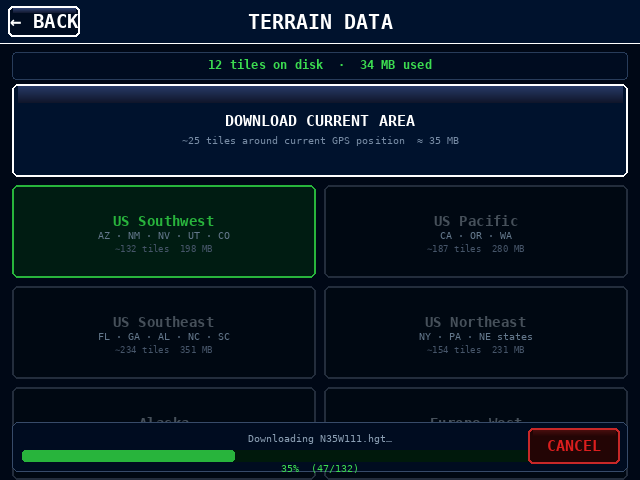
tools/preview_terrain_downloading.png
