HBDrew/PFD-and-AHRS/tools/preview_terrain_idle.png

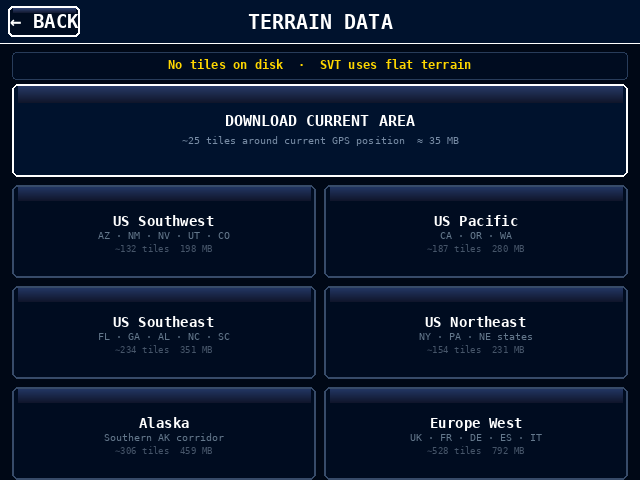
tools/preview_terrain_idle.png
