HBDrew/PFD-and-AHRS/tools/preview_vr_cascade.png

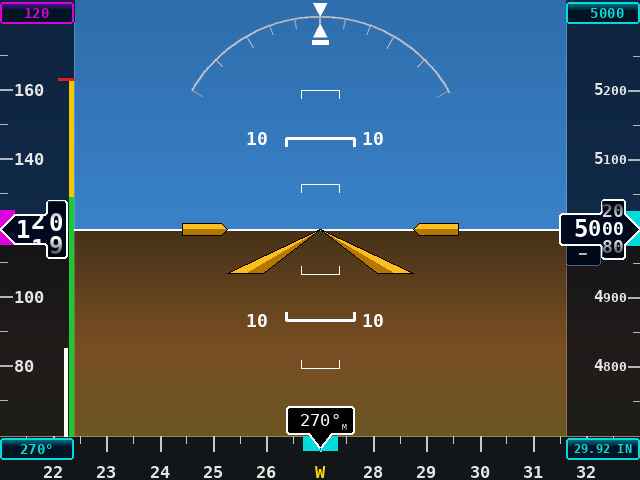
tools/preview_vr_cascade.png
