HBDrew/PFD-and-AHRS/pi4/previews/preview_setup_display.png

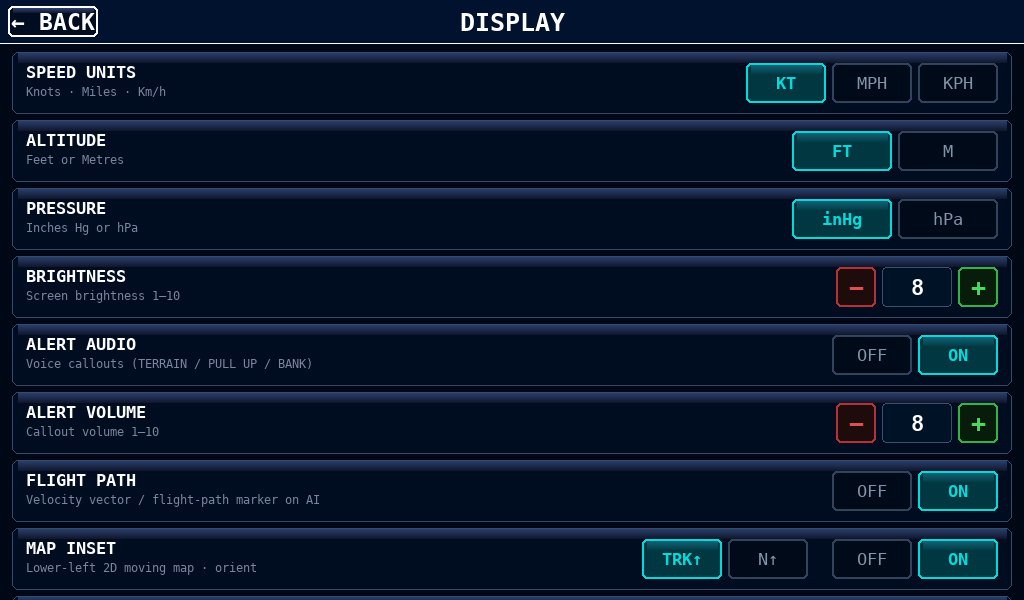
pi4/previews/preview_setup_display.png
