HBDrew/PFD-and-AHRS/tools/preview_setup_ahrs.png

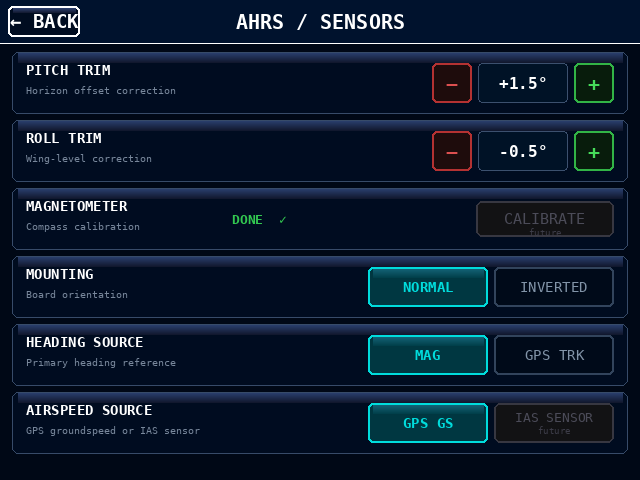
tools/preview_setup_ahrs.png
