HBDrew/PFD-and-AHRS/tools/preview_setup_connectivity.png

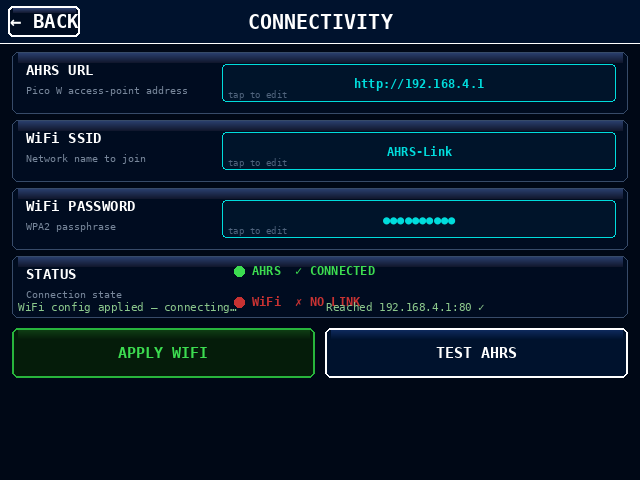
tools/preview_setup_connectivity.png
