HBDrew/PFD-and-AHRS/tools/preview_setup_display.png

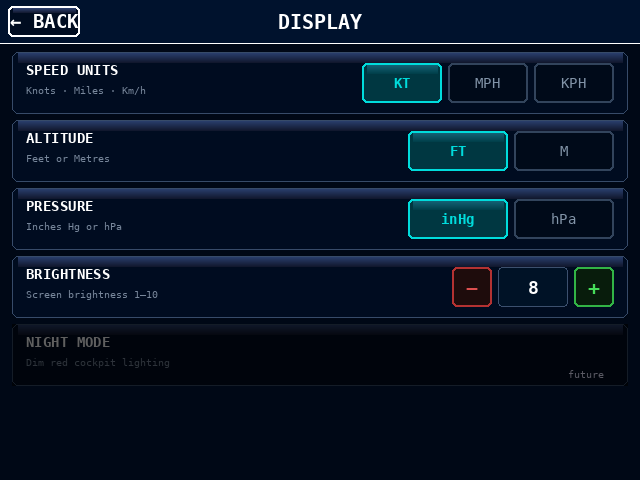
tools/preview_setup_display.png
