HBDrew/PFD-and-AHRS/tools/preview_setup_main.png

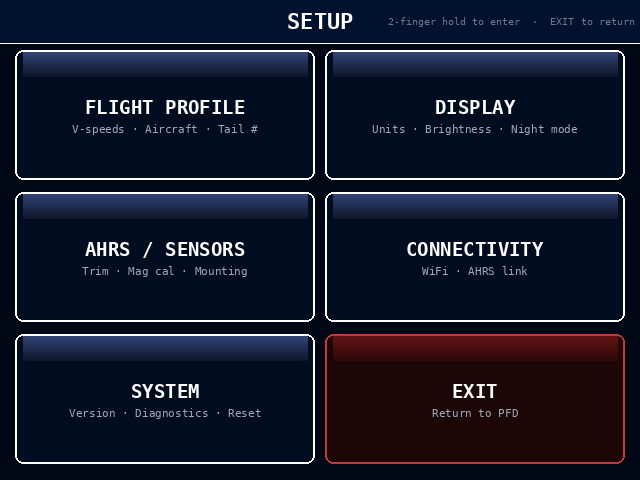
tools/preview_setup_main.png
