HBDrew/PFD-and-AHRS/pi4/previews/svt_gl_test/svt_gl_approach.png

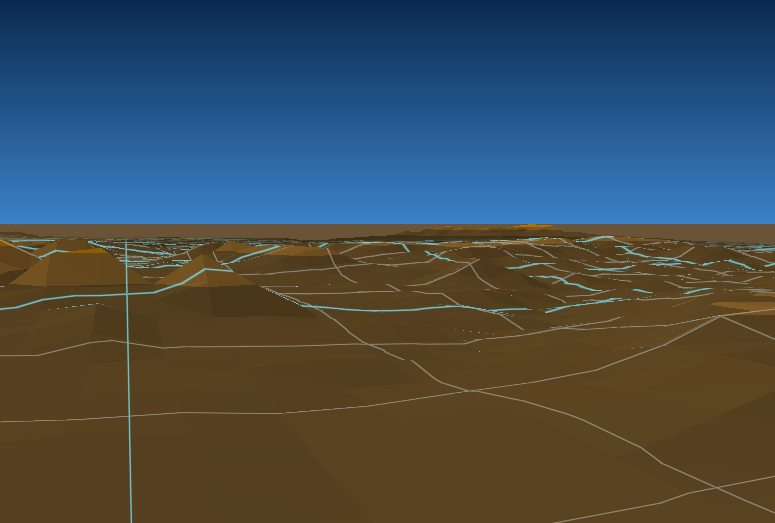
pi4/previews/svt_gl_test/svt_gl_approach.png
