HBDrew/PFD-and-AHRS/pi4/previews/svt_gl_test/svt_gl_climb_left.png

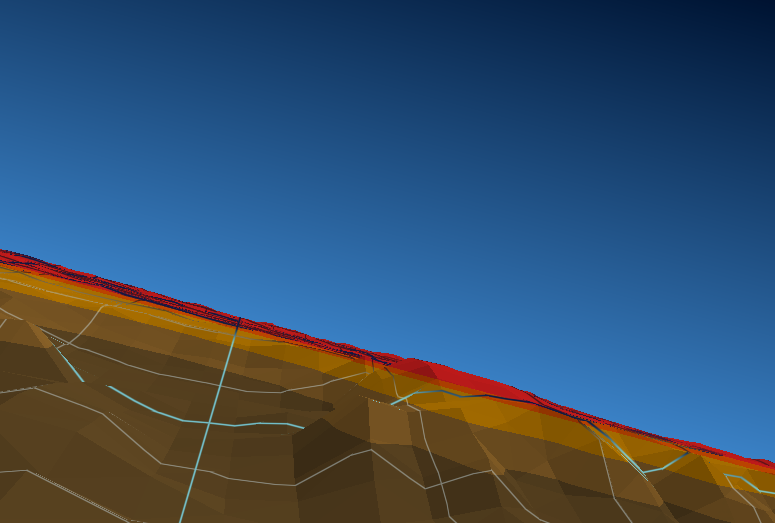
pi4/previews/svt_gl_test/svt_gl_climb_left.png
