HBDrew/PFD-and-AHRS/pi4/previews/svt_gl_test/svt_gl_flagstaff_view.png

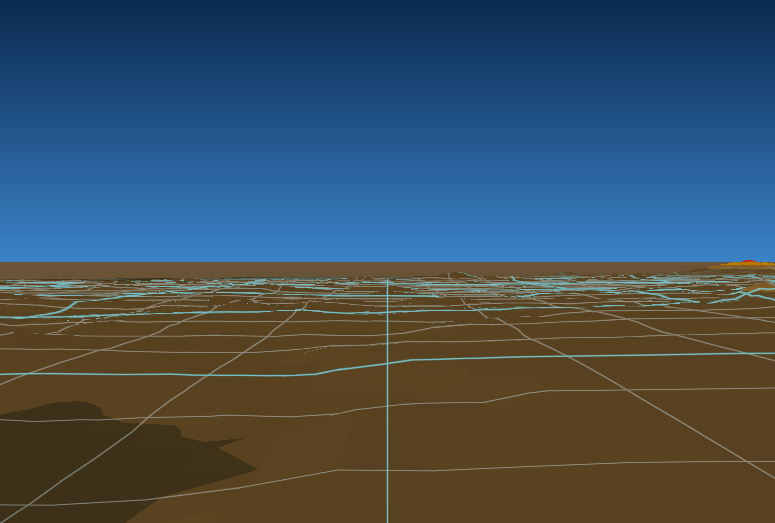
pi4/previews/svt_gl_test/svt_gl_flagstaff_view.png
