HBDrew/PFD-and-AHRS/shared/config_base.py

"""
config_base.py – Shared configuration for both Pi Zero 2W and Pi 4 display versions.

Contains V-speed defaults, barometric defaults, AHRS connection settings,
terrain/obstacle thresholds, demo presets, and flight simulator airports.

Platform-specific settings (display resolution, layout, rendering options)
are in each platform's own config.py which imports from this file.
"""

# ── Server ────────────────────────────────────────────────────────────────────
PICO_URL    = "http://192.168.4.1"        # Pico W AP address
SSE_URL     = PICO_URL + "/events"
SSE_TIMEOUT = 10                          # seconds before reconnect

# ── V-speeds (knots) – Cessna 172S defaults ───────────────────────────────────
VS0  =  48   # Stall speed, flaps down
VS1  =  55   # Stall speed, clean
VFE  =  85   # Max flap extension
VNO  = 129   # Max structural cruising
VNE  = 163   # Never exceed
VA   = 105   # Maneuvering (at gross)
VY   =  74   # Best rate of climb
VX   =  62   # Best angle of climb

# ── Barometric defaults ───────────────────────────────────────────────────────
BARO_DEFAULT_HPA = 1013.25

# ── Terrain / SVT thresholds ──────────────────────────────────────────────────
# Aligned with PALETTE_RELATIVE in shared/terrain.py — caution kicks in at the
# amber band, warning at the red band, so the central alert banner colour
# tracks the SVT terrain colour the pilot is already looking at.
TERRAIN_CAUTION_FT = 700    # terrain within 700 ft → amber alert (yellow band)
TERRAIN_WARNING_FT = 200    # terrain within 200 ft → red alert (red band)

# ── Obstacle database (FAA DOF) ───────────────────────────────────────────────
OBSTACLE_RADIUS_NM   = 5.0    # AI symbol render radius — beyond a few miles
                              # towers are too small to read and crowd the view
OBSTACLE_BELOW_FT    = 1000   # hide towers more than this far below aircraft
                              # (towers at or above us are always shown)
OBSTACLE_WINDOW_FT   = OBSTACLE_BELOW_FT  # back-compat alias — older code
                                          # used a symmetric ±window, the new
                                          # semantic is "below only" and
                                          # OBSTACLE_BELOW_FT is the source
                                          # of truth.  Kept so pi_zero keeps
                                          # importing without churn.
OBSTACLE_CAUTION_FT  = 500    # amber below this clearance
OBSTACLE_WARNING_FT  = 200    # red below this clearance — matches
                              # TERRAIN_WARNING_FT so the obstacle and
                              # terrain palettes flip to red on the same
                              # 200 ft buffer.
# Forward-look half-angle for the obstacle alert wedge. Bearings beyond
# this delta from the GPS ground track are filtered out — a tower 90°
# off the wingtip isn't a hazard and shouldn't fire the callout. ±25°
# is the middle of standard GA TAWS-B implementations (Honeywell EGPWS
# uses ±15° near-field expanding to ±30° at distance; we use a flat
# half-angle for simplicity since our look-ahead radius is already
# small relative to that ±15→30° dilation envelope).
OBSTACLE_WEDGE_HALF_DEG = 25.0
OBSTACLE_EXPIRY_DAYS = 28     # FAA DOF update cycle (days)

# ── Airport database (OurAirports CSV) ────────────────────────────────────────
AIRPORT_RADIUS_NM    = 20.0   # only show airports within this radius on AI
AIRPORT_LABEL_NM     = 15.0   # only show text label within this closer range
AIRPORT_EXPIRY_DAYS  = 60     # recommend refresh after 60 days (loose vs DOF's 28)

# ── ADS-B IN (GDL90 traffic) ──────────────────────────────────────────────────
# The display consumes GDL90 datagrams over UDP — the format emitted by a
# Nooelec NESDR Nano 2 dual-band receiver (1090ES + 978 UAT) feeding
# dump1090/dump978 through a GDL90 bridge, identical to Stratux's broadcast.
ADSB_UDP_PORT  = 4000     # conventional GDL90 broadcast port
ADSB_STALE_S   = 60       # drop a target after this long with no update
ADSB_PROX_NM   = 6.0      # proximate-traffic range envelope (amber)
ADSB_PROX_FT   = 1200     # proximate-traffic altitude envelope
ADSB_ALERT_NM  = 3.0      # (legacy) static alert range ring — no longer gates
                          #   the RA tier; kept for signature compatibility
ADSB_ALERT_FT  = 600      # alert vertical protected band (RA only fires when
                          #   the target is within this rel-alt and closing)
# Closure/time-based RA (replaces the old flat 3 NM/600 ft ring, which
# nuisance-tripped on parallel / diverging traffic).  Fire "Traffic, Traffic"
# only when a target is actually converging and will be close soon.
ADSB_TAU_S         = 30.0  # alert when time-to-zero-range (range/closure) ≤ this
ADSB_ALERT_FLOOR_NM = 1.0  # hard backstop ring — alert inside this regardless
ADSB_ALERT_FLOOR_FT = 400  #   of closure (something right on top of us)
# RA hysteresis (stops boundary chatter / audio re-trigger on borderline traffic)
ADSB_RA_ARM_S  = 0.7       # raw alert must persist this long before the RA fires
ADSB_RA_HOLD_S = 8.0       # once fired, latch the red cue this long so it stays up

# Always-on "safety" traffic clamp.  Traffic is drawn on every map page for
# situational awareness — but on the non-traffic overlays (airspace / METAR /
# NEXRAD) and the PFD inset it's clamped to *nearby* targets only, so distant
# aircraft don't clutter a weather picture.  The dedicated TFC overlay lifts
# the clamp and shows everything (still subject to the declutter filters).
# Alert-class threats are NEVER clamped out.
TRAFFIC_SAFETY_NM = 7.0   # a few miles
TRAFFIC_SAFETY_FT = 3000  # a few thousand feet

# ── Traffic source (built-in internet feed) ───────────────────────────────────
# The display always listens for GDL90/UDP (radio / SDR bridge).  It can ALSO
# run an internal internet feed so traffic works without a separate script.
# traffic_source: "auto" (feed on) | "radio" (feed off, external only) |
# "internet" (feed on).  Cycled by tapping the ADS-B label on the MFD.
TRAFFIC_FEED_SOURCE   = "airplanes_live"   # aggregator (airplanes_live/adsb_lol/adsb_fi)
TRAFFIC_FEED_RADIUS_NM = 80
TRAFFIC_FEED_INTERVAL_S = 8

# ── Weather (internet METARs; NEXRAD + FIS-B later) ───────────────────────────
# Pulled from aviationweather.gov (free, no key) around the *map view* (so
# panning/zooming over CONUS loads weather for wherever you're looking, not
# just near the aircraft).  Needs internet (AHRS on USB, or everything on a
# shared Starlink LAN).
WX_RADIUS_NM     = 150    # fallback query radius
WX_MIN_RADIUS_NM = 60     # floor — always pull at least this much context
WX_MAX_RADIUS_NM = 250    # cap — biggest single query (AWC-friendly)
WX_RADIUS_ZOOM_K = 1.8    # query radius = map range × this (clamped min/max)
WX_INTERVAL_S    = 120    # periodic refresh cadence (METARs update ~hourly)
TAF_INTERVAL_S   = 600    # TAF refresh cadence (forecasts reissue ~6 h)
AIRSIG_INTERVAL_S = 300   # AIRMET/SIGMET refresh cadence (~hourly, but watch updates)
# ── Winds aloft — one coarse NATIONAL grid, fetched rarely, cached on disk ─────
# GFS pressure-level winds only refresh every ~6 h, and we only draw barbs at the
# widest (160 nm) zoom where a coarse grid is plenty.  So instead of chasing the
# map view (which got us rate-limited — Open-Meteo meters by locations, and we
# were re-pulling on every move / restart), we pull ONE coarse coordinate-list
# grid covering CONUS in a single call (the API allows up to 1000 locations;
# ~100 nm spacing over CONUS is ~450 points), cache it to disk, and just
# read/decimate the in-view subset.  No per-move/zoom refetch.
WINDS_US_BBOX         = (24.0, 50.0, -125.0, -66.0)  # min/max lat, min/max lon (CONUS)
WINDS_US_SPACING_NM   = 60         # coarse grid spacing — ~16-24 barbs at the 160 nm view
WINDS_INET_INTERVAL_S = 6 * 3600   # GFS reissues every ~6 h — refresh no faster
WINDS_MAX_ALT_FT      = 18000      # cap — fewer pressure levels = a much cheaper call
WINDS_MIN_RENDER_NM   = 40         # draw barbs at 40/80/160 nm; hide below (coarse grid → empty)
WINDS_ZOOMS_NM        = [40, 80, 160]  # the WND page keeps its OWN zoom, limited to these
WINDS_GFS_MODEL       = "gfs025"   # pressure levels require an explicit GFS model
WINDS_DISK_MAX_AGE_S  = 3 * 3600   # a zone is "stale" after 3 h — GFS only reissues
                                   # every ~6 h, so this is plenty fresh and cuts
                                   # the per-IP call volume (esp. with >1 display).
                                   # (when connected); within the hour we read disk.
WINDS_ROUTE_WIDTH_NM  = 25         # (legacy) winds corridor half-width — unused by the national grid
NOTAM_INTERVAL_S = 600    # NOTAM refresh cadence (FAA API; only polled with a key)
# NOTAMs are far denser than METAR stations, so they use their own — much
# tighter — radius than the weather layers: a 60-100 nm weather ring over a
# metro returns hundreds of mostly-irrelevant NOTAMs.  Follows map zoom.
NOTAM_MIN_RADIUS_NM = 10   # floor — keep the local field(s) covered when zoomed in
NOTAM_MAX_RADIUS_NM = 40   # cap — biggest NOTAM query (keeps the list readable)
NOTAM_RADIUS_ZOOM_K = 1.5  # query radius = map range × this (clamped min/max)
NOTAM_CHUNK_BYTES = 1000   # max NOTAM text per screen-sync packet — keep each
                           # datagram under the network MTU so it doesn't IP-
                           # fragment (fragmented UDP broadcast drops on WiFi)
NOTAM_REBROADCAST_S = 120  # keepalive floor for re-broadcasting NOTAMs to peers.
                           # We publish IMMEDIATELY whenever a fetch changes our
                           # data; this is only the redundant resend cadence so a
                           # peer that joins/restarts between our ~10 min fetches
                           # is still fed within this window.  Kept long because a
                           # resend of unchanged data is pure dedupe churn.
NOTAM_LIST_MAX = 100       # cap the NOTAM readout to the nearest N to the tapped
                           # station (the store keeps them all; the picker shows
                           # the nearest, with a "+N more" footer — nothing hidden)
NEXRAD_INTERVAL_S = 300   # radar refresh cadence (NEXRAD updates ~5 min)
NEXRAD_MAX_PX     = 480   # fetched raster long-side px (decode/scale cost)

# ── Proximity alert lookahead ─────────────────────────────────────────────────
ALERT_TIME_S         = 60     # lookahead window in seconds
ALERT_RADIUS_MIN_NM  = 1.0    # floor — always check at least this far ahead
ALERT_RADIUS_MAX_NM  = 3.0    # ceiling — never exceed this radius

# ── Demo mode ─────────────────────────────────────────────────────────────────
DEMO_LAT = 34.8697
DEMO_LON = -111.7610
DEMO_ALT = 8500.0   # ft MSL starting altitude
DEMO_HDG = 133.0    # degrees

# ── Flight simulator presets ─────────────────────────────────────────────────
# Each entry: (icao, city_label, lat, lon, field_elev_ft)
SIM_PRESETS = [
    ("KSEZ", "Sedona AZ",        34.8486, -111.7884, 4830),
    ("KPHX", "Phoenix AZ",       33.4373, -112.0078, 1135),
    ("KDEN", "Denver CO",        39.8561, -104.6737, 5431),
    ("KLAX", "Los Angeles CA",   33.9425, -118.4081,  125),
    ("KSFO", "San Francisco CA", 37.6213, -122.3790,   13),
    ("KLAS", "Las Vegas NV",     36.0840, -115.1537, 2141),
    ("KSEA", "Seattle WA",       47.4502, -122.3088,  433),
    ("KOSH", "Oshkosh WI",       43.9844,  -88.5570,  808),
    ("KJFK", "New York NY",      40.6413,  -73.7781,   13),
    ("KORD", "Chicago IL",       41.9742,  -87.9073,  668),
    ("KDFW", "Dallas TX",        32.8998,  -97.0403,  603),
    ("KMIA", "Miami FL",         25.7959,  -80.2870,    8),
]

# ── Touch / interaction ───────────────────────────────────────────────────────
LONG_PRESS_MS    = 800  # ms for 2-finger long-press to enter setup
MFD_SWAP_HOLD_MS = 2000 # ms for 3-finger hold to swap PFD ↔ MFD on piZ
STALE_TIMEOUT_S  = 3    # seconds after link loss before AHRS is marked failed

# ── GPS heading complementary filter ─────────────────────────────────────────
GPS_HDG_SLAVE_K  = 0.05
