HBDrew/PFD-and-AHRS/shared/magvar.py

"""World Magnetic Model 2025 — magnetic declination (variation) only.

The whole EFIS is internally TRUE-referenced: GPS track is true, the
magnetometer is calibrated against true cardinals, and every stored course
(approach course, flight-plan leg bearing) is a true great-circle bearing.
Charts, plates, runway numbers and ATC clearances are MAGNETIC, so for the
pilot-facing display we convert true -> magnetic with the local variation.

This module provides that variation from the WMM2025 spherical-harmonic model
(valid 2025.0–2030.0).  It is self-contained: the degree-12 Gauss coefficients
are embedded below, so there is no data file to ship to each Pi and no network
dependency.

Convention: declination east-positive (the usual aviation sense).  In Arizona
it is ~+10–11° (east), so a true bearing of 041° reads ~030° magnetic.

    magnetic = true - declination_east

Coefficients: NOAA/NGA World Magnetic Model 2025 (public domain).
Computation vendored and trimmed to declination-only from pygeomag
(https://pypi.org/project/pygeomag/, MIT, © 2023 Justin Myers), which in turn
follows the WMM reference C implementation.
"""

import math
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
